vossstef/tang_nano_20k_c64/.assets/dolphin.png

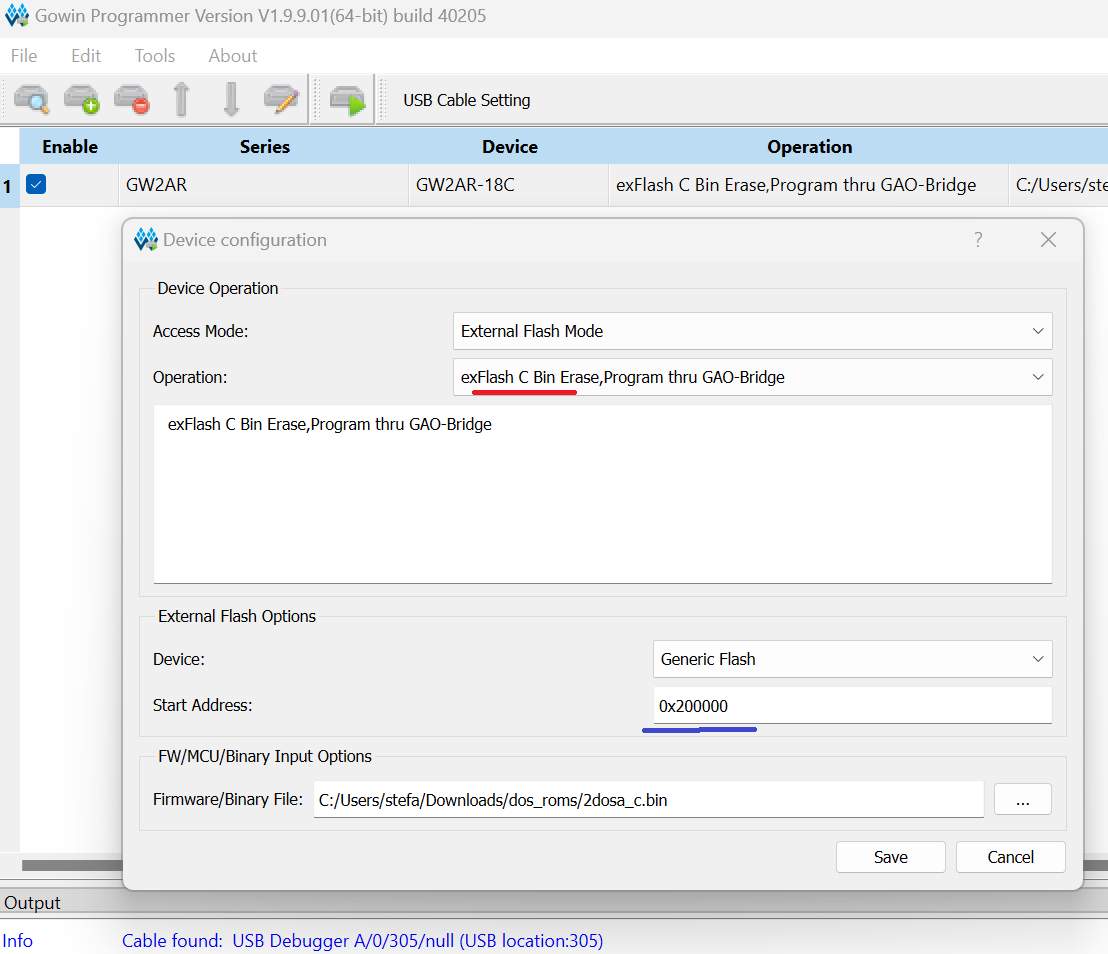
.assets/dolphin.png
