vossstef/tang_nano_20k_c64/.assets/PS_connnector_female.png

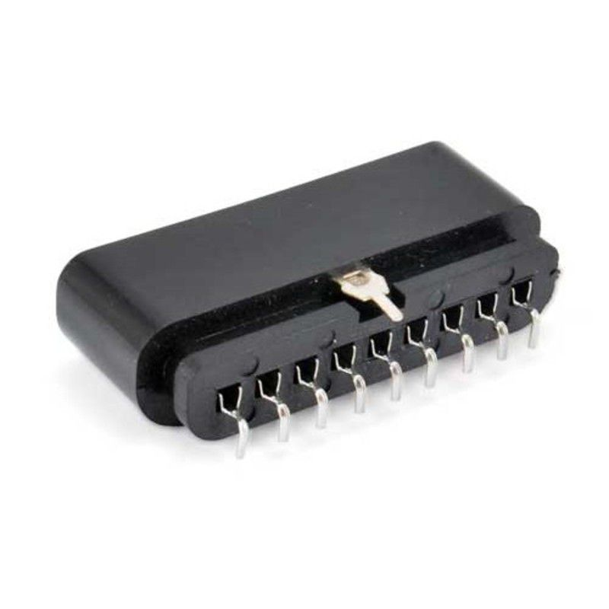
.assets/PS_connnector_female.png
