vossstef/tang_nano_20k_c64/.assets/vic20-Joystick.png

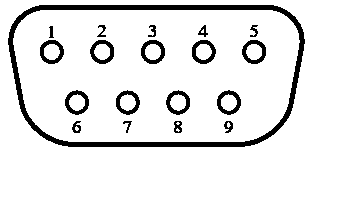
.assets/vic20-Joystick.png
