vossstef/tang_nano_20k_c64/src/fifo_sc_hs/FIFO_SC_HS_Top_gw5a.vhd

--
--Written by GowinSynthesis
--Tool Version "V1.9.9.01"
--Sun May 12 00:47:38 2024

--Source file index table:
--file0 "\/home/vossstef/Dokumente/tang_nano_20k_c64/src/fifo_sc_hs/temp/FIFO_SC/fifo_sc_hs_define.v"
--file1 "\/home/vossstef/Dokumente/tang_nano_20k_c64/src/fifo_sc_hs/temp/FIFO_SC/fifo_sc_hs_parameter.v"
--file2 "\/home/vossstef/Gowin_V1.9.9.01_linux/IDE/ipcore/FIFO_SC_HS/data/fifo_sc_hs.v"
--file3 "\/home/vossstef/Gowin_V1.9.9.01_linux/IDE/ipcore/FIFO_SC_HS/data/fifo_sc_hs_top.v"
`protect begin_protected
`protect version="2.3"
`protect author="default"
`protect author_info="default"
`protect encrypt_agent="GOWIN"
`protect encrypt_agent_info="GOWIN Encrypt Version 2.3"

`protect encoding=(enctype="base64", line_length=76, bytes=256)
`protect key_keyowner="GOWIN",key_keyname="GWK2023-09",key_method="rsa"
`protect key_block
fKtc7d56dFamvtFDO4O6QlQ/mQChC2vDqB9vvZFQsu07QmbTZwBCbHcSg9c2Qbw2vTp5auoD3b91
VnBrmFIJE7ZO6ixMmp+q2YNrsiA/RSfsNSDEhH0vKQw0LDGQ+LaQpbsQsP38Ywhr5HGWnS7MoDNv
HSwKX9g8mJT7/Q4Lo8iNRCs/QKyWcXytIdWEIsB2yFttuY125pkIy0eVJklfc4fd11sZIxdmgucz
9DaDS1XFvY0Kz34P5/p6mjfi3PbE+sys5c+FAVy7ctopbtMai24WShkPhMkbUDM6WWXWU74ohBRx
wu/SC8lLKIqFNhuwDpfDWYbmTo6930i3iSJX9w==

`protect encoding=(enctype="base64", line_length=76, bytes=15648)
`protect data_keyowner="default-ip-vendor"
`protect data_keyname="default-ip-key"
`protect data_method="aes128-cfb"
`protect data_block
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
`protect end_protected
library ieee;
use ieee.std_logic_1164.all;
use ieee.numeric_std.all;
library gw5a;
use gw5a.components.all;

entity FIFO_SC_HS_Top is
port(
  Data :  in std_logic_vector(7 downto 0);
  Clk :  in std_logic;
  WrEn :  in std_logic;
  RdEn :  in std_logic;
  Reset :  in std_logic;
  Q :  out std_logic_vector(7 downto 0);
  Empty :  out std_logic;
  Full :  out std_logic);
end FIFO_SC_HS_Top;
architecture beh of FIFO_SC_HS_Top is
  signal GND_0 : std_logic ;
  signal VCC_0 : std_logic ;
  signal NN : std_logic;
  signal NN_0 : std_logic;
component \~fifo_sc_hs.FIFO_SC_HS_Top\
port(
  Clk: in std_logic;
  Reset: in std_logic;
  VCC_0: in std_logic;
  GND_0: in std_logic;
  WrEn: in std_logic;
  RdEn: in std_logic;
  Data : in std_logic_vector(7 downto 0);
  Full: out std_logic;
  Empty: out std_logic;
  Q : out std_logic_vector(7 downto 0));
end component;
begin
GND_s0: GND
port map (
  G => GND_0);
VCC_s0: VCC
port map (
  V => VCC_0);
GSR_0: GSR
port map (
  GSRI => VCC_0);
fifo_sc_hs_inst: \~fifo_sc_hs.FIFO_SC_HS_Top\
port map(
  Clk => Clk,
  Reset => Reset,
  VCC_0 => VCC_0,
  GND_0 => GND_0,
  WrEn => WrEn,
  RdEn => RdEn,
  Data(7 downto 0) => Data(7 downto 0),
  Full => NN_0,
  Empty => NN,
  Q(7 downto 0) => Q(7 downto 0));
  Empty <= NN;
  Full <= NN_0;
end beh;
