vossstef/tang_nano_20k_c64/src/fifo_sc_hs/fifo_sc_hs.vhd

--
--Written by GowinSynthesis
--Tool Version "V1.9.9.03 (64-bit)"
--Mon Jul  8 15:35:15 2024

--Source file index table:
--file0 "\C:/Users/stefa/Documents/tang_nano_20k_c64/src/fifo_sc_hs/temp/FIFO_SC/fifo_sc_hs_define.v"
--file1 "\C:/Users/stefa/Documents/tang_nano_20k_c64/src/fifo_sc_hs/temp/FIFO_SC/fifo_sc_hs_parameter.v"
--file2 "\C:/Gowin/Gowin_V1.9.9.03_x64/IDE/ipcore/FIFO_SC_HS/data/fifo_sc_hs.v"
--file3 "\C:/Gowin/Gowin_V1.9.9.03_x64/IDE/ipcore/FIFO_SC_HS/data/fifo_sc_hs_top.v"
`protect begin_protected
`protect version="2.3"
`protect author="default"
`protect author_info="default"
`protect encrypt_agent="GOWIN"
`protect encrypt_agent_info="GOWIN Encrypt Version 2.3"

`protect encoding=(enctype="base64", line_length=76, bytes=256)
`protect key_keyowner="GOWIN",key_keyname="GWK2023-09",key_method="rsa"
`protect key_block
EqpCJ1Ww4Pd49B2vVASAo8LpiKKOyOr3fTQtoLEopzYBtsWzW9bwJBFufjYHFtUn8GTtPZPMO28v
8B5rUJs4Hd9uLl1OBi0kSgzbjz0PQjZvvBaG3FrvJm5WkEEgTZf6h/XYErPHf6a9ePw1mQcK/w0V
Tmn92XFVjoSysDTE2lJd41btgDYM6X3vHBOaUt+NLuypAHF27Vg6/a/ukPi+VDsF926BOYJWViP6
U+svy8MhF74v+ClimO5vWuc31+6F3fQYnS+kNuW+etjyU2ZvlGD7zxUmuTqySt4hpy7pKWiCeO8I
zxJ03vHaeP2blj3EFD5TOylCkKAc+X9MKyoI2g==

`protect encoding=(enctype="base64", line_length=76, bytes=12560)
`protect data_keyowner="default-ip-vendor"
`protect data_keyname="default-ip-key"
`protect data_method="aes128-cfb"
`protect data_block
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
cxmnYrtEVBrdJe5dDqL7tjZQre0=
`protect end_protected
library ieee;
use ieee.std_logic_1164.all;
use ieee.numeric_std.all;
library gw2a;
use gw2a.components.all;

entity FIFO_SC_HS_Top is
port(
  Data :  in std_logic_vector(7 downto 0);
  Clk :  in std_logic;
  WrEn :  in std_logic;
  RdEn :  in std_logic;
  Reset :  in std_logic;
  Q :  out std_logic_vector(7 downto 0);
  Empty :  out std_logic;
  Full :  out std_logic);
end FIFO_SC_HS_Top;
architecture beh of FIFO_SC_HS_Top is
  signal Clk_d : std_logic ;
  signal WrEn_d : std_logic ;
  signal RdEn_d : std_logic ;
  signal Reset_d : std_logic ;
  signal GND_0 : std_logic ;
  signal VCC_0 : std_logic ;
  signal Full_d : std_logic ;
  signal Empty_d : std_logic ;
  signal Data_d : std_logic_vector(7 downto 0);
  signal Q_d : std_logic_vector(7 downto 0);
component \~fifo_sc_hs.FIFO_SC_HS_Top\
port(
  Clk_d: in std_logic;
  Reset_d: in std_logic;
  GND_0: in std_logic;
  VCC_0: in std_logic;
  WrEn_d: in std_logic;
  RdEn_d: in std_logic;
  Data_d : in std_logic_vector(7 downto 0);
  Full_d: out std_logic;
  Empty_d: out std_logic;
  Q_d : out std_logic_vector(7 downto 0));
end component;
begin
Data_0_ibuf: IBUF
port map (
  O => Data_d(0),
  I => Data(0));
Data_1_ibuf: IBUF
port map (
  O => Data_d(1),
  I => Data(1));
Data_2_ibuf: IBUF
port map (
  O => Data_d(2),
  I => Data(2));
Data_3_ibuf: IBUF
port map (
  O => Data_d(3),
  I => Data(3));
Data_4_ibuf: IBUF
port map (
  O => Data_d(4),
  I => Data(4));
Data_5_ibuf: IBUF
port map (
  O => Data_d(5),
  I => Data(5));
Data_6_ibuf: IBUF
port map (
  O => Data_d(6),
  I => Data(6));
Data_7_ibuf: IBUF
port map (
  O => Data_d(7),
  I => Data(7));
Clk_ibuf: IBUF
port map (
  O => Clk_d,
  I => Clk);
WrEn_ibuf: IBUF
port map (
  O => WrEn_d,
  I => WrEn);
RdEn_ibuf: IBUF
port map (
  O => RdEn_d,
  I => RdEn);
Reset_ibuf: IBUF
port map (
  O => Reset_d,
  I => Reset);
Q_0_obuf: OBUF
port map (
  O => Q(0),
  I => Q_d(0));
Q_1_obuf: OBUF
port map (
  O => Q(1),
  I => Q_d(1));
Q_2_obuf: OBUF
port map (
  O => Q(2),
  I => Q_d(2));
Q_3_obuf: OBUF
port map (
  O => Q(3),
  I => Q_d(3));
Q_4_obuf: OBUF
port map (
  O => Q(4),
  I => Q_d(4));
Q_5_obuf: OBUF
port map (
  O => Q(5),
  I => Q_d(5));
Q_6_obuf: OBUF
port map (
  O => Q(6),
  I => Q_d(6));
Q_7_obuf: OBUF
port map (
  O => Q(7),
  I => Q_d(7));
Empty_obuf: OBUF
port map (
  O => Empty,
  I => Empty_d);
Full_obuf: OBUF
port map (
  O => Full,
  I => Full_d);
GND_s0: GND
port map (
  G => GND_0);
VCC_s0: VCC
port map (
  V => VCC_0);
GSR_0: GSR
port map (
  GSRI => VCC_0);
fifo_sc_hs_inst: \~fifo_sc_hs.FIFO_SC_HS_Top\
port map(
  Clk_d => Clk_d,
  Reset_d => Reset_d,
  GND_0 => GND_0,
  VCC_0 => VCC_0,
  WrEn_d => WrEn_d,
  RdEn_d => RdEn_d,
  Data_d(7 downto 0) => Data_d(7 downto 0),
  Full_d => Full_d,
  Empty_d => Empty_d,
  Q_d(7 downto 0) => Q_d(7 downto 0));
end beh;
