vossstef/tang_nano_20k_c64/src/sid/sid_tables.sv

module sid_tables
#(
	parameter MULTI_FILTERS   = 1
)
(
	input             clock,
	input             mode,

	// waves
	input      [11:0] acc_t,
	output reg  [7:0] _st_out,
	output reg  [7:0] p_t_out,
	output reg  [7:0] ps__out,
	output reg  [7:0] pst_out,

	// filter
	input       [1:0] cfg,
	input      [10:0] Fc,
	input      [12:0] Fc_offset,
	output     [15:0] F0,
	input             ld_clk,
	input      [11:0] ld_addr,
	input      [15:0] ld_data,
	input             ld_wr
);

// P + T
always_ff @(posedge clock) begin
	p_t_out <= mode ? wave8580_p_t[acc_t[10:0]] : wave6581_p_t[acc_t[10:0]];
end

// P + S
always_ff @(posedge clock) begin
	ps__out <= mode ? wave8580_ps_[acc_t] : wave6581_ps_[acc_t[10:0]];
end

// S + T
always_ff @(posedge clock) begin
	_st_out <= mode ? {
		((acc_t & 'he7e) == 'he7e) | ((acc_t & 'he80) == 'he80) | ((acc_t & 'hf00) == 'hf00) | ((acc_t & 'he7d) == 'he7d),
		((acc_t & 'h7f8) == 'h7f8) | ((acc_t & 'hf00) == 'hf00),
		((acc_t & 'h7e0) == 'h7e0) | ((acc_t & 'hf0f) == 'hf0f) | ((acc_t & 'hf1b) == 'hf1b) | ((acc_t & 'hbfe) == 'hbfe) | ((acc_t & 'hf1e) == 'hf1e) | ((acc_t & 'hf40) == 'hf40) | ((acc_t & 'hf30) == 'hf30) | ((acc_t & 'hf29) == 'hf29) | ((acc_t & 'hf26) == 'hf26) | ((acc_t & 'hf80) == 'hf80),
		((acc_t & 'h7e0) == 'h7e0) | ((acc_t & 'h3f0) == 'h3f0) | ((acc_t & 'hdfe) == 'hdfe) | ((acc_t & 'h5ff) == 'h5ff) | ((acc_t & 'hf80) == 'hf80),
		((acc_t & 'h7e0) == 'h7e0) | ((acc_t & 'h3f0) == 'h3f0) | ((acc_t & 'hfc0) == 'hfc0) | ((acc_t & 'h1f8) == 'h1f8) | ((acc_t & 'heff) == 'heff),
		((acc_t & 'h0fc) == 'h0fc) | ((acc_t & 'h1f8) == 'h1f8) | ((acc_t & 'h3f0) == 'h3f0) | ((acc_t & 'hfe0) == 'hfe0),
		((acc_t & 'h07e) == 'h07e) | ((acc_t & 'hff0) == 'hff0) | ((acc_t & 'h7f7) == 'h7f7) | ((acc_t & 'h1f8) == 'h1f8) | ((acc_t & 'h0fc) == 'h0fc),
		((acc_t & 'hdbf) == 'hdbf) | ((acc_t & 'h0fc) == 'h0fc) | ((acc_t & 'h3fa) == 'h3fa) | ((acc_t & 'h7f8) == 'h7f8) | ((acc_t & 'h3bf) == 'h3bf) | ((acc_t & 'h07e) == 'h07e)
	} : {
		1'b0,
		((acc_t & 'h7fc) == 'h7fc),
		((acc_t & 'h7e0) == 'h7e0) | ((acc_t & 'h3fe) == 'h3fe),
		((acc_t & 'h7e0) == 'h7e0) | ((acc_t & 'h5ff) == 'h5ff) | ((acc_t & 'h3f0) == 'h3f0),
		((acc_t & 'h7e0) == 'h7e0) | ((acc_t & 'h1f8) == 'h1f8) | ((acc_t & 'h3f0) == 'h3f0),
		((acc_t & 'h0fc) == 'h0fc) | ((acc_t & 'h1f8) == 'h1f8) | ((acc_t & 'h3f0) == 'h3f0),
		((acc_t & 'h07e) == 'h07e) | ((acc_t & 'h1f8) == 'h1f8) | ((acc_t & 'h0fc) == 'h0fc),
		((acc_t & 'h13f) == 'h13f) | ((acc_t & 'h07e) == 'h07e) | ((acc_t & 'h7fa) == 'h7fa) | ((acc_t & 'h0bf) == 'h0bf) | ((acc_t & 'h0fc) == 'h0fc)
	};
end

// P + S + T
always_ff @(posedge clock) begin
	pst_out <= mode ? {
		((acc_t & 'he89) == 'he89) | ((acc_t & 'he3e) == 'he3e) | ((acc_t & 'hec0) == 'hec0) | ((acc_t & 'he8a) == 'he8a) | ((acc_t & 'hdf7) == 'hdf7) | ((acc_t & 'hdf8) == 'hdf8) | ((acc_t & 'he85) == 'he85) | ((acc_t & 'he6a) == 'he6a) | ((acc_t & 'he90) == 'he90) | ((acc_t & 'he83) == 'he83) | ((acc_t & 'he67) == 'he67) | ((acc_t & 'hea0) == 'hea0) | ((acc_t & 'hf00) == 'hf00) | ((acc_t & 'he5e) == 'he5e) | ((acc_t & 'he70) == 'he70) | ((acc_t & 'he6c) == 'he6c),
		((acc_t & 'heee) == 'heee) | ((acc_t & 'h7ef) == 'h7ef) | ((acc_t & 'h7f2) == 'h7f2) | ((acc_t & 'h7f4) == 'h7f4) | ((acc_t & 'hef0) == 'hef0) | ((acc_t & 'h7f8) == 'h7f8) | ((acc_t & 'hf00) == 'hf00) | ((acc_t & 'h7f1) == 'h7f1),
		((acc_t & 'hf78) == 'hf78) | ((acc_t & 'h7f0) == 'h7f0) | ((acc_t & 'h7ee) == 'h7ee) | ((acc_t & 'hf74) == 'hf74) | ((acc_t & 'hf6f) == 'hf6f) | ((acc_t & 'hf80) == 'hf80) | ((acc_t & 'hbff) == 'hbff),
		((acc_t & 'hdff) == 'hdff) | ((acc_t & 'hbfe) == 'hbfe) | ((acc_t & 'h7ef) == 'h7ef) | ((acc_t & 'h7f2) == 'h7f2) | ((acc_t & 'h3ff) == 'h3ff) | ((acc_t & 'h7f4) == 'h7f4) | ((acc_t & 'hfc0) == 'hfc0) | ((acc_t & 'hfb8) == 'hfb8) | ((acc_t & 'h7f8) == 'h7f8) | ((acc_t & 'hfb6) == 'hfb6),
		((acc_t & 'hbfe) == 'hbfe) | ((acc_t & 'hfdc) == 'hfdc) | ((acc_t & 'hdfe) == 'hdfe) | ((acc_t & 'h7f7) == 'h7f7) | ((acc_t & 'hfda) == 'hfda) | ((acc_t & 'hbfd) == 'hbfd) | ((acc_t & 'h7f8) == 'h7f8) | ((acc_t & 'h3ff) == 'h3ff) | ((acc_t & 'hfe0) == 'hfe0) | ((acc_t & 'heff) == 'heff),
		((acc_t & 'hfeb) == 'hfeb) | ((acc_t & 'h7fa) == 'h7fa) | ((acc_t & 'hbfe) == 'hbfe) | ((acc_t & 'hdfe) == 'hdfe) | ((acc_t & 'hff0) == 'hff0) | ((acc_t & 'h7fc) == 'h7fc) | ((acc_t & 'h3ff) == 'h3ff) | ((acc_t & 'hfec) == 'hfec) | ((acc_t & 'heff) == 'heff),
		((acc_t & 'hff6) == 'hff6) | ((acc_t & 'hdff) == 'hdff) | ((acc_t & 'hf7f) == 'hf7f) | ((acc_t & 'hbfe) == 'hbfe) | ((acc_t & 'h7fc) == 'h7fc) | ((acc_t & 'hff5) == 'hff5) | ((acc_t & 'h3ff) == 'h3ff) | ((acc_t & 'hff8) == 'hff8) | ((acc_t & 'heff) == 'heff),
		((acc_t & 'hdff) == 'hdff) | ((acc_t & 'hf7f) == 'hf7f) | ((acc_t & 'hffa) == 'hffa) | ((acc_t & 'h7fe) == 'h7fe) | ((acc_t & 'hff9) == 'hff9) | ((acc_t & 'hffc) == 'hffc) | ((acc_t & 'h3ff) == 'h3ff) | ((acc_t & 'heff) == 'heff)
	} : {
		1'b0,
		((acc_t & 'h7fc) == 'h7fc) | ((acc_t & 'h7fb) == 'h7fb),
		((acc_t & 'h7ef) == 'h7ef) | ((acc_t & 'h7f7) == 'h7f7) | ((acc_t & 'h7fc) == 'h7fc) | ((acc_t & 'h7fb) == 'h7fb) | ((acc_t & 'h3ff) == 'h3ff),
		((acc_t & 'h7fc) == 'h7fc) | ((acc_t & 'h3ff) == 'h3ff) | ((acc_t & 'h7f7) == 'h7f7) | ((acc_t & 'h7fb) == 'h7fb),
		((acc_t & 'h7fc) == 'h7fc) | ((acc_t & 'h3ff) == 'h3ff) | ((acc_t & 'h7fb) == 'h7fb),
		((acc_t & 'h7fd) == 'h7fd) | ((acc_t & 'h3ff) == 'h3ff) | ((acc_t & 'h7fe) == 'h7fe),
		((acc_t & 'h7fd) == 'h7fd) | ((acc_t & 'h3ff) == 'h3ff) | ((acc_t & 'h7fe) == 'h7fe),
		((acc_t & 'h3ff) == 'h3ff) | ((acc_t & 'h7fe) == 'h7fe)
	};
end


wire [7:0] wave6581_p_t[0:2047] = 
'{
	'h00, 'h00, 'h00, 'h00, 'h00, 'h00, 'h00, 'h00, 'h00, 'h00, 'h00, 'h00, 'h00, 'h00, 'h00, 'h00,
	'h00, 'h00, 'h00, 'h00, 'h00, 'h00, 'h00, 'h00, 'h00, 'h00, 'h00, 'h00, 'h00, 'h00, 'h00, 'h00,
	'h00, 'h00, 'h00, 'h00, 'h00, 'h00, 'h00, 'h00, 'h00, 'h00, 'h00, 'h00, 'h00, 'h00, 'h00, 'h00,
	'h00, 'h00, 'h00, 'h00, 'h00, 'h00, 'h00, 'h00, 'h00, 'h00, 'h00, 'h00, 'h00, 'h00, 'h00, 'h00,
	'h00, 'h00, 'h00, 'h00, 'h00, 'h00, 'h00, 'h00, 'h00, 'h00, 'h00, 'h00, 'h00, 'h00, 'h00, 'h00,
	'h00, 'h00, 'h00, 'h00, 'h00, 'h00, 'h00, 'h00, 'h00, 'h00, 'h00, 'h00, 'h00, 'h00, 'h00, 'h00,
	'h00, 'h00, 'h00, 'h00, 'h00, 'h00, 'h00, 'h00, 'h00, 'h00, 'h00, 'h00, 'h00, 'h00, 'h00, 'h00,
	'h00, 'h00, 'h00, 'h00, 'h00, 'h00, 'h00, 'h00, 'h00, 'h00, 'h00, 'h00, 'h00, 'h00, 'h00, 'h00,
	'h00, 'h00, 'h00, 'h00, 'h00, 'h00, 'h00, 'h00, 'h00, 'h00, 'h00, 'h00, 'h00, 'h00, 'h00, 'h00,
	'h00, 'h00, 'h00, 'h00, 'h00, 'h00, 'h00, 'h00, 'h00, 'h00, 'h00, 'h00, 'h00, 'h00, 'h00, 'h00,
	'h00, 'h00, 'h00, 'h00, 'h00, 'h00, 'h00, 'h00, 'h00, 'h00, 'h00, 'h00, 'h00, 'h00, 'h00, 'h00,
	'h00, 'h00, 'h00, 'h00, 'h00, 'h00, 'h00, 'h00, 'h00, 'h00, 'h00, 'h00, 'h00, 'h00, 'h00, 'h00,
	'h00, 'h00, 'h00, 'h00, 'h00, 'h00, 'h00, 'h00, 'h00, 'h00, 'h00, 'h00, 'h00, 'h00, 'h00, 'h00,
	'h00, 'h00, 'h00, 'h00, 'h00, 'h00, 'h00, 'h00, 'h00, 'h00, 'h00, 'h00, 'h00, 'h00, 'h00, 'h00,
	'h00, 'h00, 'h00, 'h00, 'h00, 'h00, 'h00, 'h00, 'h00, 'h00, 'h00, 'h00, 'h00, 'h00, 'h00, 'h00,
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
	'h00, 'h00, 'h00, 'h00, 'h00, 'h00, 'h00, 'h00, 'h00, 'h00, 'h00, 'h00, 'h00, 'h00, 'h00, 'h80,
	'h00, 'h00, 'h00, 'h00, 'h00, 'h00, 'h00, 'h80, 'h00, 'h00, 'h00, 'h80, 'h00, 'h80, 'h80, 'hc0,
	'h00, 'h00, 'h00, 'h00, 'h00, 'h00, 'h00, 'h80, 'h00, 'h00, 'h00, 'h80, 'h00, 'h80, 'h80, 'hc0,
	'h00, 'h00, 'h00, 'h80, 'h00, 'h80, 'hc0, 'hc0, 'h80, 'hc0, 'hc0, 'hc0, 'hc0, 'hc0, 'hd0, 'hd7,
	'h00, 'h00, 'h00, 'h00, 'h00, 'h00, 'h00, 'h80, 'h00, 'h00, 'h00, 'h80, 'h80, 'h80, 'hc0, 'hc0,
	'h00, 'h80, 'h80, 'hc0, 'h80, 'hc0, 'hc0, 'hc0, 'h80, 'hc0, 'hc0, 'hc0, 'hc0, 'hd0, 'hd0, 'hdb,
	'h00, 'h80, 'h80, 'hc0, 'h80, 'hc0, 'hc0, 'hd0, 'h80, 'hc0, 'hc0, 'hd0, 'hc0, 'hd0, 'hd8, 'hdd,
	'hc0, 'hc0, 'hc0, 'hd0, 'hc0, 'hd8, 'hd8, 'hde, 'hc0, 'hd8, 'hdc, 'hdf, 'hdc, 'hdf, 'hdf, 'hdf,
	'h00, 'h00, 'h00, 'h00, 'h00, 'h00, 'h00, 'h00, 'h00, 'h00, 'h00, 'h00, 'h00, 'h00, 'h00, 'h80,
	'h00, 'h00, 'h00, 'h00, 'h00, 'h00, 'h00, 'h80, 'h00, 'h00, 'h00, 'h80, 'h80, 'hc0, 'hc0, 'he0,
	'h00, 'h00, 'h00, 'h00, 'h00, 'h00, 'h00, 'h80, 'h00, 'h80, 'h80, 'hc0, 'h80, 'hc0, 'hc0, 'he0,
	'h00, 'h80, 'h80, 'hc0, 'h80, 'hc0, 'hc0, 'he0, 'h80, 'hc0, 'hc0, 'he0, 'hc0, 'he0, 'he0, 'he7,
	'h00, 'h00, 'h00, 'h80, 'h00, 'h80, 'h80, 'hc0, 'h00, 'h80, 'h80, 'hc0, 'h80, 'hc0, 'hc0, 'he0,
	'h00, 'h80, 'h80, 'hc0, 'h80, 'hc0, 'hc0, 'he0, 'hc0, 'hc0, 'hc0, 'he0, 'he0, 'he0, 'he0, 'heb,
	'h80, 'h80, 'hc0, 'hc0, 'hc0, 'hc0, 'hc0, 'he0, 'hc0, 'he0, 'he0, 'he0, 'he0, 'he0, 'he0, 'hed,
	'hc0, 'he0, 'he0, 'he0, 'he0, 'he8, 'he8, 'hee, 'he0, 'he8, 'hec, 'hef, 'hec, 'hef, 'hef, 'hef,
	'h00, 'h00, 'h00, 'h80, 'h80, 'h80, 'h80, 'hc0, 'h80, 'h80, 'hc0, 'hc0, 'hc0, 'hc0, 'hc0, 'hf0,
	'h80, 'hc0, 'hc0, 'hc0, 'hc0, 'he0, 'he0, 'hf0, 'hc0, 'he0, 'he0, 'hf0, 'he0, 'hf0, 'hf0, 'hf3,
	'h80, 'hc0, 'hc0, 'he0, 'hc0, 'he0, 'he0, 'hf0, 'hc0, 'he0, 'he0, 'hf0, 'he0, 'hf0, 'hf0, 'hf5,
	'he0, 'he0, 'he0, 'hf0, 'hf0, 'hf0, 'hf0, 'hf6, 'hf0, 'hf0, 'hf4, 'hf7, 'hf4, 'hf7, 'hf7, 'hf7,
	'hc0, 'hc0, 'hc0, 'he0, 'he0, 'he0, 'he0, 'hf0, 'he0, 'he0, 'he0, 'hf8, 'hf0, 'hf8, 'hf8, 'hf9,
	'he0, 'hf0, 'hf0, 'hf8, 'hf0, 'hf8, 'hf8, 'hfa, 'hf0, 'hf8, 'hf8, 'hfb, 'hf8, 'hfb, 'hfb, 'hfb,
	'he0, 'hf0, 'hf0, 'hf8, 'hf0, 'hf8, 'hfc, 'hfc, 'hf8, 'hfc, 'hfc, 'hfd, 'hfc, 'hfd, 'hfd, 'hfd,
	'hf8, 'hfc, 'hfe, 'hfe, 'hfe, 'hfe, 'hfe, 'hfe, 'hfe, 'hff, 'hff, 'hff, 'hff, 'hff, 'hff, 'hff
};


wire [7:0] wave6581_ps_[0:2047] = 
'{
	'h00, 'h00, 'h00, 'h00, 'h00, 'h00, 'h00, 'h00, 'h00, 'h00, 'h00, 'h00, 'h00, 'h00, 'h00, 'h00,
	'h00, 'h00, 'h00, 'h00, 'h00, 'h00, 'h00, 'h00, 'h00, 'h00, 'h00, 'h00, 'h00, 'h00, 'h00, 'h00,
	'h00, 'h00, 'h00, 'h00, 'h00, 'h00, 'h00, 'h00, 'h00, 'h00, 'h00, 'h00, 'h00, 'h00, 'h00, 'h00,
	'h00, 'h00, 'h00, 'h00, 'h00, 'h00, 'h00, 'h00, 'h00, 'h00, 'h00, 'h00, 'h00, 'h00, 'h00, 'h00,
	'h00, 'h00, 'h00, 'h00, 'h00, 'h00, 'h00, 'h00, 'h00, 'h00, 'h00, 'h00, 'h00, 'h00, 'h00, 'h00,
	'h00, 'h00, 'h00, 'h00, 'h00, 'h00, 'h00, 'h00, 'h00, 'h00, 'h00, 'h00, 'h00, 'h00, 'h00, 'h00,
	'h00, 'h00, 'h00, 'h00, 'h00, 'h00, 'h00, 'h00, 'h00, 'h00, 'h00, 'h00, 'h00, 'h00, 'h00, 'h00,
	'h00, 'h00, 'h00, 'h00, 'h00, 'h00, 'h00, 'h00, 'h00, 'h00, 'h00, 'h00, 'h00, 'h00, 'h00, 'h00,
	'h00, 'h00, 'h00, 'h00, 'h00, 'h00, 'h00, 'h00, 'h00, 'h00, 'h00, 'h00, 'h00, 'h00, 'h00, 'h00,
	'h00, 'h00, 'h00, 'h00, 'h00, 'h00, 'h00, 'h00, 'h00, 'h00, 'h00, 'h00, 'h00, 'h00, 'h00, 'h00,
	'h00, 'h00, 'h00, 'h00, 'h00, 'h00, 'h00, 'h00, 'h00, 'h00, 'h00, 'h00, 'h00, 'h00, 'h00, 'h00,
	'h00, 'h00, 'h00, 'h00, 'h00, 'h00, 'h00, 'h00, 'h00, 'h00, 'h00, 'h00, 'h00, 'h00, 'h00, 'h00,
	'h00, 'h00, 'h00, 'h00, 'h00, 'h00, 'h00, 'h00, 'h00, 'h00, 'h00, 'h00, 'h00, 'h00, 'h00, 'h00,
	'h00, 'h00, 'h00, 'h00, 'h00, 'h00, 'h00, 'h00, 'h00, 'h00, 'h00, 'h00, 'h00, 'h00, 'h00, 'h00,
	'h00, 'h00, 'h00, 'h00, 'h00, 'h00, 'h00, 'h00, 'h00, 'h00, 'h00, 'h00, 'h00, 'h00, 'h00, 'h00,
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
	'h80, 'h80, 'h80, 'h80, 'h80, 'h80, 'h80, 'h80, 'h80, 'h80, 'h80, 'h80, 'h80, 'h80, 'h80, 'hc0,
	'h80, 'h80, 'h80, 'h80, 'h80, 'h80, 'hc0, 'hc0, 'h80, 'hc0, 'hc0, 'hc0, 'hc0, 'hc0, 'hc0, 'hc3,
	'h80, 'h80, 'h80, 'h80, 'h80, 'h80, 'h80, 'hc0, 'h80, 'h80, 'h80, 'hc0, 'h80, 'hc0, 'hc0, 'hc0,
	'h80, 'hc0, 'hc0, 'hc0, 'hc0, 'hc0, 'hc0, 'hc0, 'hc0, 'hc0, 'hc0, 'hc0, 'hc0, 'hc0, 'hc0, 'hc1,
	'hc0, 'hc0, 'hc0, 'hc0, 'hc0, 'hc0, 'hc0, 'hc0, 'hc0, 'hc0, 'hc0, 'hc0, 'hc0, 'hc0, 'hc0, 'hc0,
	'hc0, 'hc0, 'hc0, 'hc0, 'hc0, 'hc0, 'hc0, 'hc0, 'hc0, 'hc0, 'hc0, 'hc0, 'hc0, 'hc1, 'hc7, 'hd7,
	'hc0, 'hc0, 'hc0, 'hc0, 'hc0, 'hc0, 'hc0, 'hc0, 'hc0, 'hc0, 'hc0, 'hc0, 'hc0, 'hc0, 'hc0, 'hc0,
	'hc0, 'hc0, 'hc0, 'hc0, 'hc0, 'hc0, 'hc0, 'hc0, 'hc0, 'hc0, 'hc0, 'hc0, 'hc0, 'hc0, 'hc0, 'hc0,
	'hc0, 'hc0, 'hc0, 'hc0, 'hc0, 'hc0, 'hc0, 'hc0, 'hc0, 'hc0, 'hc0, 'hc0, 'hc0, 'hc0, 'hc0, 'hd0,
	'hc0, 'hc0, 'hc0, 'hc0, 'hc0, 'hc0, 'hc0, 'hd0, 'hc0, 'hc0, 'hc0, 'hd0, 'hc0, 'hd0, 'hd8, 'hdb,
	'hc0, 'hc0, 'hc0, 'hc0, 'hc0, 'hc0, 'hc0, 'hc0, 'hc0, 'hc0, 'hc0, 'hc0, 'hc0, 'hc0, 'hc0, 'hd8,
	'hc0, 'hc0, 'hc0, 'hc0, 'hc0, 'hc0, 'hc0, 'hd8, 'hc0, 'hc0, 'hc0, 'hd8, 'hd0, 'hd8, 'hd8, 'hdd,
	'hc0, 'hc0, 'hc0, 'hd0, 'hc0, 'hd0, 'hd0, 'hdc, 'hd0, 'hd8, 'hd8, 'hdc, 'hd8, 'hdc, 'hdc, 'hde,
	'hd8, 'hdc, 'hdc, 'hde, 'hdc, 'hde, 'hde, 'hdf, 'hde, 'hdf, 'hdf, 'hdf, 'hdf, 'hdf, 'hdf, 'hdf,
	'hc0, 'hc0, 'hc0, 'hc0, 'hc0, 'hc0, 'hc0, 'hc0, 'hc0, 'hc0, 'hc0, 'hc0, 'hc0, 'hc0, 'hc0, 'hc0,
	'hc0, 'hc0, 'hc0, 'hc0, 'hc0, 'hc0, 'hc0, 'hc0, 'hc0, 'hc0, 'hc0, 'hc0, 'hc0, 'hc0, 'hc0, 'hc0,
	'hc0, 'hc0, 'hc0, 'hc0, 'hc0, 'hc0, 'hc0, 'hc0, 'hc0, 'hc0, 'hc0, 'hc0, 'hc0, 'hc0, 'hc0, 'hc0,
	'hc0, 'hc0, 'hc0, 'hc0, 'hc0, 'hc0, 'hc0, 'hc0, 'hc0, 'hc0, 'hc0, 'hc0, 'hc0, 'hc0, 'hc0, 'he3,
	'hc0, 'hc0, 'hc0, 'hc0, 'hc0, 'hc0, 'hc0, 'hc0, 'hc0, 'hc0, 'hc0, 'hc0, 'hc0, 'hc0, 'hc0, 'hc0,
	'hc0, 'hc0, 'hc0, 'hc0, 'hc0, 'hc0, 'hc0, 'he0, 'hc0, 'hc0, 'hc0, 'he0, 'hc0, 'he0, 'he0, 'he1,
	'hc0, 'hc0, 'hc0, 'hc0, 'hc0, 'hc0, 'hc0, 'he0, 'hc0, 'hc0, 'hc0, 'he0, 'he0, 'he0, 'he0, 'he0,
	'hc0, 'he0, 'he0, 'he0, 'he0, 'he0, 'he0, 'he0, 'he0, 'he0, 'he0, 'he0, 'he0, 'he1, 'he3, 'he7,
	'hc0, 'hc0, 'hc0, 'hc0, 'hc0, 'hc0, 'hc0, 'he0, 'hc0, 'hc0, 'hc0, 'he0, 'hc0, 'he0, 'he0, 'he0,
	'hc0, 'hc0, 'hc0, 'he0, 'hc0, 'he0, 'he0, 'he0, 'he0, 'he0, 'he0, 'he0, 'he0, 'he0, 'he0, 'he0,
	'he0, 'he0, 'he0, 'he0, 'he0, 'he0, 'he0, 'he0, 'he0, 'he0, 'he0, 'he0, 'he0, 'he0, 'he0, 'he0,
	'he0, 'he0, 'he0, 'he0, 'he0, 'he0, 'he0, 'he0, 'he0, 'he0, 'he0, 'he0, 'he0, 'he0, 'he0, 'heb,
	'he0, 'he0, 'he0, 'he0, 'he0, 'he0, 'he0, 'he0, 'he0, 'he0, 'he0, 'he0, 'he0, 'he0, 'he0, 'he0,
	'he0, 'he0, 'he0, 'he0, 'he0, 'he0, 'he0, 'he0, 'he0, 'he0, 'he0, 'he8, 'he0, 'he8, 'he8, 'hed,
	'he0, 'he0, 'he0, 'he0, 'he0, 'he0, 'he0, 'hec, 'he0, 'he0, 'he0, 'hec, 'he8, 'hec, 'hec, 'hee,
	'he8, 'he8, 'he8, 'hec, 'hec, 'hee, 'hee, 'hef, 'hec, 'hef, 'hef, 'hef, 'hef, 'hef, 'hef, 'hef,
	'he0, 'he0, 'he0, 'he0, 'he0, 'he0, 'he0, 'he0, 'he0, 'he0, 'he0, 'he0, 'he0, 'he0, 'he0, 'he0,
	'he0, 'he0, 'he0, 'he0, 'he0, 'he0, 'he0, 'he0, 'he0, 'he0, 'he0, 'he0, 'he0, 'he0, 'he0, 'hf0,
	'he0, 'he0, 'he0, 'he0, 'he0, 'he0, 'he0, 'hf0, 'he0, 'he0, 'he0, 'hf0, 'he0, 'hf0, 'hf0, 'hf0,
	'he0, 'he0, 'he0, 'hf0, 'hf0, 'hf0, 'hf0, 'hf0, 'hf0, 'hf0, 'hf0, 'hf0, 'hf0, 'hf0, 'hf0, 'hf3,
	'he0, 'he0, 'he0, 'hf0, 'hf0, 'hf0, 'hf0, 'hf0, 'hf0, 'hf0, 'hf0, 'hf0, 'hf0, 'hf0, 'hf0, 'hf0,
	'hf0, 'hf0, 'hf0, 'hf0, 'hf0, 'hf0, 'hf0, 'hf0, 'hf0, 'hf0, 'hf0, 'hf0, 'hf0, 'hf0, 'hf0, 'hf5,
	'hf0, 'hf0, 'hf0, 'hf0, 'hf0, 'hf0, 'hf0, 'hf0, 'hf0, 'hf0, 'hf0, 'hf0, 'hf0, 'hf4, 'hf4, 'hf6,
	'hf0, 'hf0, 'hf0, 'hf4, 'hf0, 'hf4, 'hf6, 'hf7, 'hf4, 'hf6, 'hf6, 'hf7, 'hf7, 'hf7, 'hf7, 'hf7,
	'hf0, 'hf0, 'hf0, 'hf0, 'hf0, 'hf0, 'hf0, 'hf8, 'hf0, 'hf0, 'hf0, 'hf0, 'hf0, 'hf8, 'hf8, 'hf8,
	'hf0, 'hf0, 'hf0, 'hf8, 'hf0, 'hf8, 'hf8, 'hf8, 'hf8, 'hf8, 'hf8, 'hf8, 'hf8, 'hf8, 'hf8, 'hf9,
	'hf8, 'hf8, 'hf8, 'hf8, 'hf8, 'hf8, 'hf8, 'hf8, 'hf8, 'hf8, 'hf8, 'hf8, 'hf8, 'hf8, 'hf8, 'hfa,
	'hf8, 'hf8, 'hf8, 'hf8, 'hf8, 'hf8, 'hf8, 'hfb, 'hf8, 'hfa, 'hfa, 'hfb, 'hfb, 'hfb, 'hfb, 'hfb,
	'hf8, 'hf8, 'hf8, 'hfc, 'hf8, 'hfc, 'hfc, 'hfc, 'hfc, 'hfc, 'hfc, 'hfc, 'hfc, 'hfc, 'hfc, 'hfc,
	'hfc, 'hfc, 'hfc, 'hfc, 'hfc, 'hfc, 'hfc, 'hfd, 'hfc, 'hfc, 'hfc, 'hfd, 'hfd, 'hfd, 'hfd, 'hfd,
	'hfc, 'hfc, 'hfe, 'hfe, 'hfe, 'hfe, 'hfe, 'hfe, 'hfe, 'hfe, 'hfe, 'hfe, 'hfe, 'hfe, 'hfe, 'hfe,
	'hff, 'hff, 'hff, 'hff, 'hff, 'hff, 'hff, 'hff, 'hff, 'hff, 'hff, 'hff, 'hff, 'hff, 'hff, 'hff
};


/////////////////////////////////////////////////////////////////////////////////////


reg [15:0] f0;
generate
	if(MULTI_FILTERS) begin
		always_ff @(posedge ld_clk) if(ld_wr) f6581_curve[1024+ld_addr] <= ld_data;
		always_ff @(posedge clock) f0 <= f6581_curve[{cfg, Fc[10:1]}];
	end
	else begin
		always_ff @(posedge ld_clk) if(ld_wr) f6581_curve[ld_addr[9:0]] <= ld_data;
		always_ff @(posedge clock) f0 <= f6581_curve[Fc[10:1]];
	end
endgenerate

wire [10:0] fc_6581;
sid_dac #(.BITS(11)) fc_dac
(
  .vin  (Fc),
  .vout (fc_6581)
);

function reg [9:0] tanh_x_mirror(signed [10:0] x);
    tanh_x_mirror = 10'(x < 0 ? -x : x);
endfunction

function signed [10:0] tanh_x_clamp(signed [12:0] x);
    tanh_x_clamp = (x < -1023) ? -11'sd1023 :
                   (x >  1023) ?  11'sd1023 :
                   11'(x);
endfunction

function signed [15:0] tanh_y_mirror(logic x_neg,signed [15:0] y);
    tanh_y_mirror = x_neg ? -y : y;
endfunction

wire signed [15:0] f6581_adj_y0 = 16'(9883+250);
wire [10:0] fc_x = tanh_x_clamp(13'(fc_6581) - Fc_offset);

reg [15:0] f0_adj;
always_ff @(posedge clock) f0_adj <= {fc_x[10], f6581_adj[tanh_x_mirror(fc_x)]};

assign F0 = mode ? ({ 3'b000, Fc, 2'b00 } + Fc) : Fc_offset ? (f6581_adj_y0 + tanh_y_mirror(f0_adj[15], f0_adj[14:0])) : {1'b0, f0[15:1]};

// value = pi * 1.048576 * f0[fc]
reg  [15:0] f6581_curve[4*1024] =
'{
	// 0 mixed calc 
      933,    932,    932,    933,    936,    937,    943,    948,
      949,    945,    936,    926,    920,    918,    920,    924,
      930,    938,    945,    954,    960,    960,    955,    951,
      950,    949,    948,    948,    948,    945,    945,    945,
      948,    943,    942,    937,    937,    937,    939,    945,
      950,    951,    956,    960,    965,    971,    977,    981,
      982,    979,    976,    970,    964,    957,    949,    944,
      942,    942,    945,    950,    955,    955,    957,    960,
      961,    957,    954,    948,    948,    949,    955,    958,
      964,    971,    975,    979,    981,    979,    979,    975,
      973,    971,    970,    969,    969,    969,    969,    973,
      973,    971,    967,    965,    965,    963,    963,    967,
      970,    976,    987,    995,   1001,    996,    993,    987,
      983,    982,    984,    988,    992,    992,    994,    999,
      999,    994,    988,    981,    982,    988,   1002,   1014,
     1020,   1018,   1008,   1000,    994,    996,    997,   1005,
     1009,   1008,   1006,   1002,   1005,   1006,   1012,   1018,
     1024,   1024,   1024,   1024,   1026,   1027,   1029,   1033,
     1035,   1033,   1029,   1026,   1027,   1029,   1035,   1041,
     1047,   1048,   1047,   1048,   1053,   1059,   1072,   1082,
     1086,   1078,   1063,   1047,   1041,   1045,   1057,   1069,
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
    6687,   6702,   6717,   6732,   6748,   6763,   6778,   6793,
    6807,   6822,   6837,   6852,   6866,   6881,   6895,   6910,
    6924,   6939,   6953,   6967,   6981,   6995,   7009,   7023,
    7037,   7051,   7065,   7079,   7093,   7106,   7120,   7133,
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
};

endmodule
