vossstef/tang_nano_20k_c64/src/gowin_prom/gowin_prom_basic.vhd

--Copyright (C)2014-2024 Gowin Semiconductor Corporation.
--All rights reserved.
--File Title: IP file
--Tool Version: V1.9.9.02
--Part Number: GW2AR-LV18QN88C8/I7
--Device: GW2AR-18
--Device Version: C
--Created Time: Thu Apr 25 13:04:41 2024

library IEEE;
use IEEE.std_logic_1164.all;

entity Gowin_pROM_basic is
    port (
        dout: out std_logic_vector(7 downto 0);
        clk: in std_logic;
        oce: in std_logic;
        ce: in std_logic;
        reset: in std_logic;
        ad: in std_logic_vector(12 downto 0)
    );
end Gowin_pROM_basic;

architecture Behavioral of Gowin_pROM_basic is

    signal prom_inst_0_dout_w: std_logic_vector(29 downto 0);
    signal prom_inst_1_dout_w: std_logic_vector(29 downto 0);
    signal prom_inst_2_dout_w: std_logic_vector(29 downto 0);
    signal prom_inst_3_dout_w: std_logic_vector(29 downto 0);
    signal gw_gnd: std_logic;
    signal prom_inst_0_AD_i: std_logic_vector(13 downto 0);
    signal prom_inst_0_DO_o: std_logic_vector(31 downto 0);
    signal prom_inst_1_AD_i: std_logic_vector(13 downto 0);
    signal prom_inst_1_DO_o: std_logic_vector(31 downto 0);
    signal prom_inst_2_AD_i: std_logic_vector(13 downto 0);
    signal prom_inst_2_DO_o: std_logic_vector(31 downto 0);
    signal prom_inst_3_AD_i: std_logic_vector(13 downto 0);
    signal prom_inst_3_DO_o: std_logic_vector(31 downto 0);

    --component declaration
    component pROM
        generic (
            READ_MODE: in bit :='0';
            BIT_WIDTH: in integer := 1;
            RESET_MODE: in string := "SYNC";
            INIT_RAM_00: in bit_vector := X"0000000000000000000000000000000000000000000000000000000000000000";
            INIT_RAM_01: in bit_vector := X"0000000000000000000000000000000000000000000000000000000000000000";
            INIT_RAM_02: in bit_vector := X"0000000000000000000000000000000000000000000000000000000000000000";
            INIT_RAM_03: in bit_vector := X"0000000000000000000000000000000000000000000000000000000000000000";
            INIT_RAM_04: in bit_vector := X"0000000000000000000000000000000000000000000000000000000000000000";
            INIT_RAM_05: in bit_vector := X"0000000000000000000000000000000000000000000000000000000000000000";
            INIT_RAM_06: in bit_vector := X"0000000000000000000000000000000000000000000000000000000000000000";
            INIT_RAM_07: in bit_vector := X"0000000000000000000000000000000000000000000000000000000000000000";
            INIT_RAM_08: in bit_vector := X"0000000000000000000000000000000000000000000000000000000000000000";
            INIT_RAM_09: in bit_vector := X"0000000000000000000000000000000000000000000000000000000000000000";
            INIT_RAM_0A: in bit_vector := X"0000000000000000000000000000000000000000000000000000000000000000";
            INIT_RAM_0B: in bit_vector := X"0000000000000000000000000000000000000000000000000000000000000000";
            INIT_RAM_0C: in bit_vector := X"0000000000000000000000000000000000000000000000000000000000000000";
            INIT_RAM_0D: in bit_vector := X"0000000000000000000000000000000000000000000000000000000000000000";
            INIT_RAM_0E: in bit_vector := X"0000000000000000000000000000000000000000000000000000000000000000";
            INIT_RAM_0F: in bit_vector := X"0000000000000000000000000000000000000000000000000000000000000000";
            INIT_RAM_10: in bit_vector := X"0000000000000000000000000000000000000000000000000000000000000000";
            INIT_RAM_11: in bit_vector := X"0000000000000000000000000000000000000000000000000000000000000000";
            INIT_RAM_12: in bit_vector := X"0000000000000000000000000000000000000000000000000000000000000000";
            INIT_RAM_13: in bit_vector := X"0000000000000000000000000000000000000000000000000000000000000000";
            INIT_RAM_14: in bit_vector := X"0000000000000000000000000000000000000000000000000000000000000000";
            INIT_RAM_15: in bit_vector := X"0000000000000000000000000000000000000000000000000000000000000000";
            INIT_RAM_16: in bit_vector := X"0000000000000000000000000000000000000000000000000000000000000000";
            INIT_RAM_17: in bit_vector := X"0000000000000000000000000000000000000000000000000000000000000000";
            INIT_RAM_18: in bit_vector := X"0000000000000000000000000000000000000000000000000000000000000000";
            INIT_RAM_19: in bit_vector := X"0000000000000000000000000000000000000000000000000000000000000000";
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
        )
        port map (
            DO => prom_inst_3_DO_o,
            CLK => clk,
            OCE => oce,
            CE => ce,
            RESET => reset,
            AD => prom_inst_3_AD_i
        );

end Behavioral; --Gowin_pROM_basic
