vossstef/tang_nano_20k_c64/src/gowin_sdpb/gowin_sdpb_kernal_8k.vhd

--Copyright (C)2014-2024 Gowin Semiconductor Corporation.
--All rights reserved.
--File Title: IP file
--Tool Version: V1.9.9.02
--Part Number: GW2AR-LV18QN88C8/I7
--Device: GW2AR-18
--Device Version: C
--Created Time: Thu Apr 25 13:22:34 2024

library IEEE;
use IEEE.std_logic_1164.all;

entity Gowin_SDPB_kernal_8k is
    port (
        dout: out std_logic_vector(7 downto 0);
        clka: in std_logic;
        cea: in std_logic;
        reseta: in std_logic;
        clkb: in std_logic;
        ceb: in std_logic;
        resetb: in std_logic;
        oce: in std_logic;
        ada: in std_logic_vector(12 downto 0);
        din: in std_logic_vector(7 downto 0);
        adb: in std_logic_vector(12 downto 0)
    );
end Gowin_SDPB_kernal_8k;

architecture Behavioral of Gowin_SDPB_kernal_8k is

    signal sdpb_inst_0_dout_w: std_logic_vector(29 downto 0);
    signal sdpb_inst_1_dout_w: std_logic_vector(29 downto 0);
    signal sdpb_inst_2_dout_w: std_logic_vector(29 downto 0);
    signal sdpb_inst_3_dout_w: std_logic_vector(29 downto 0);
    signal gw_gnd: std_logic;
    signal sdpb_inst_0_BLKSELA_i: std_logic_vector(2 downto 0);
    signal sdpb_inst_0_BLKSELB_i: std_logic_vector(2 downto 0);
    signal sdpb_inst_0_ADA_i: std_logic_vector(13 downto 0);
    signal sdpb_inst_0_DI_i: std_logic_vector(31 downto 0);
    signal sdpb_inst_0_ADB_i: std_logic_vector(13 downto 0);
    signal sdpb_inst_0_DO_o: std_logic_vector(31 downto 0);
    signal sdpb_inst_1_BLKSELA_i: std_logic_vector(2 downto 0);
    signal sdpb_inst_1_BLKSELB_i: std_logic_vector(2 downto 0);
    signal sdpb_inst_1_ADA_i: std_logic_vector(13 downto 0);
    signal sdpb_inst_1_DI_i: std_logic_vector(31 downto 0);
    signal sdpb_inst_1_ADB_i: std_logic_vector(13 downto 0);
    signal sdpb_inst_1_DO_o: std_logic_vector(31 downto 0);
    signal sdpb_inst_2_BLKSELA_i: std_logic_vector(2 downto 0);
    signal sdpb_inst_2_BLKSELB_i: std_logic_vector(2 downto 0);
    signal sdpb_inst_2_ADA_i: std_logic_vector(13 downto 0);
    signal sdpb_inst_2_DI_i: std_logic_vector(31 downto 0);
    signal sdpb_inst_2_ADB_i: std_logic_vector(13 downto 0);
    signal sdpb_inst_2_DO_o: std_logic_vector(31 downto 0);
    signal sdpb_inst_3_BLKSELA_i: std_logic_vector(2 downto 0);
    signal sdpb_inst_3_BLKSELB_i: std_logic_vector(2 downto 0);
    signal sdpb_inst_3_ADA_i: std_logic_vector(13 downto 0);
    signal sdpb_inst_3_DI_i: std_logic_vector(31 downto 0);
    signal sdpb_inst_3_ADB_i: std_logic_vector(13 downto 0);
    signal sdpb_inst_3_DO_o: std_logic_vector(31 downto 0);

    --component declaration
    component SDPB
        generic (
            READ_MODE: in bit := '0';
            BIT_WIDTH_0: in integer :=16;
            BIT_WIDTH_1: in integer :=16;
            BLK_SEL_0: in bit_vector := "000";
            BLK_SEL_1: in bit_vector := "000";
            RESET_MODE: in string := "SYNC";
            INIT_RAM_00: in bit_vector := X"0000000000000000000000000000000000000000000000000000000000000000";
            INIT_RAM_01: in bit_vector := X"0000000000000000000000000000000000000000000000000000000000000000";
            INIT_RAM_02: in bit_vector := X"0000000000000000000000000000000000000000000000000000000000000000";
            INIT_RAM_03: in bit_vector := X"0000000000000000000000000000000000000000000000000000000000000000";
            INIT_RAM_04: in bit_vector := X"0000000000000000000000000000000000000000000000000000000000000000";
            INIT_RAM_05: in bit_vector := X"0000000000000000000000000000000000000000000000000000000000000000";
            INIT_RAM_06: in bit_vector := X"0000000000000000000000000000000000000000000000000000000000000000";
            INIT_RAM_07: in bit_vector := X"0000000000000000000000000000000000000000000000000000000000000000";
            INIT_RAM_08: in bit_vector := X"0000000000000000000000000000000000000000000000000000000000000000";
            INIT_RAM_09: in bit_vector := X"0000000000000000000000000000000000000000000000000000000000000000";
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
            BLKSELB: in std_logic_vector(2 downto 0);
            ADA: in std_logic_vector(13 downto 0);
            DI: in std_logic_vector(31 downto 0);
            ADB: in std_logic_vector(13 downto 0)
        );
    end component;

begin
    gw_gnd <= '0';

    sdpb_inst_0_BLKSELA_i <= gw_gnd & gw_gnd & gw_gnd;
    sdpb_inst_0_BLKSELB_i <= gw_gnd & gw_gnd & gw_gnd;
    sdpb_inst_0_ADA_i <= ada(12 downto 0) & gw_gnd;
    sdpb_inst_0_DI_i <= gw_gnd & gw_gnd & gw_gnd & gw_gnd & gw_gnd & gw_gnd & gw_gnd & gw_gnd & gw_gnd & gw_gnd & gw_gnd & gw_gnd & gw_gnd & gw_gnd & gw_gnd & gw_gnd & gw_gnd & gw_gnd & gw_gnd & gw_gnd & gw_gnd & gw_gnd & gw_gnd & gw_gnd & gw_gnd & gw_gnd & gw_gnd & gw_gnd & gw_gnd & gw_gnd & din(1 downto 0);
    sdpb_inst_0_ADB_i <= adb(12 downto 0) & gw_gnd;
    dout(1 downto 0) <= sdpb_inst_0_DO_o(1 downto 0) ;
    sdpb_inst_0_dout_w(29 downto 0) <= sdpb_inst_0_DO_o(31 downto 2) ;
    sdpb_inst_1_BLKSELA_i <= gw_gnd & gw_gnd & gw_gnd;
    sdpb_inst_1_BLKSELB_i <= gw_gnd & gw_gnd & gw_gnd;
    sdpb_inst_1_ADA_i <= ada(12 downto 0) & gw_gnd;
    sdpb_inst_1_DI_i <= gw_gnd & gw_gnd & gw_gnd & gw_gnd & gw_gnd & gw_gnd & gw_gnd & gw_gnd & gw_gnd & gw_gnd & gw_gnd & gw_gnd & gw_gnd & gw_gnd & gw_gnd & gw_gnd & gw_gnd & gw_gnd & gw_gnd & gw_gnd & gw_gnd & gw_gnd & gw_gnd & gw_gnd & gw_gnd & gw_gnd & gw_gnd & gw_gnd & gw_gnd & gw_gnd & din(3 downto 2);
    sdpb_inst_1_ADB_i <= adb(12 downto 0) & gw_gnd;
    dout(3 downto 2) <= sdpb_inst_1_DO_o(1 downto 0) ;
    sdpb_inst_1_dout_w(29 downto 0) <= sdpb_inst_1_DO_o(31 downto 2) ;
    sdpb_inst_2_BLKSELA_i <= gw_gnd & gw_gnd & gw_gnd;
    sdpb_inst_2_BLKSELB_i <= gw_gnd & gw_gnd & gw_gnd;
    sdpb_inst_2_ADA_i <= ada(12 downto 0) & gw_gnd;
    sdpb_inst_2_DI_i <= gw_gnd & gw_gnd & gw_gnd & gw_gnd & gw_gnd & gw_gnd & gw_gnd & gw_gnd & gw_gnd & gw_gnd & gw_gnd & gw_gnd & gw_gnd & gw_gnd & gw_gnd & gw_gnd & gw_gnd & gw_gnd & gw_gnd & gw_gnd & gw_gnd & gw_gnd & gw_gnd & gw_gnd & gw_gnd & gw_gnd & gw_gnd & gw_gnd & gw_gnd & gw_gnd & din(5 downto 4);
    sdpb_inst_2_ADB_i <= adb(12 downto 0) & gw_gnd;
    dout(5 downto 4) <= sdpb_inst_2_DO_o(1 downto 0) ;
    sdpb_inst_2_dout_w(29 downto 0) <= sdpb_inst_2_DO_o(31 downto 2) ;
    sdpb_inst_3_BLKSELA_i <= gw_gnd & gw_gnd & gw_gnd;
    sdpb_inst_3_BLKSELB_i <= gw_gnd & gw_gnd & gw_gnd;
    sdpb_inst_3_ADA_i <= ada(12 downto 0) & gw_gnd;
    sdpb_inst_3_DI_i <= gw_gnd & gw_gnd & gw_gnd & gw_gnd & gw_gnd & gw_gnd & gw_gnd & gw_gnd & gw_gnd & gw_gnd & gw_gnd & gw_gnd & gw_gnd & gw_gnd & gw_gnd & gw_gnd & gw_gnd & gw_gnd & gw_gnd & gw_gnd & gw_gnd & gw_gnd & gw_gnd & gw_gnd & gw_gnd & gw_gnd & gw_gnd & gw_gnd & gw_gnd & gw_gnd & din(7 downto 6);
    sdpb_inst_3_ADB_i <= adb(12 downto 0) & gw_gnd;
    dout(7 downto 6) <= sdpb_inst_3_DO_o(1 downto 0) ;
    sdpb_inst_3_dout_w(29 downto 0) <= sdpb_inst_3_DO_o(31 downto 2) ;

    sdpb_inst_0: SDPB
        generic map (
            READ_MODE => '0',
            BIT_WIDTH_0 => 2,
            BIT_WIDTH_1 => 2,
            RESET_MODE => "SYNC",
            BLK_SEL_0 => "000",
            BLK_SEL_1 => "000",
            INIT_RAM_00 => X"1445216085A804D5F21600D120DE21490D113070306524545614C534083054C9",
            INIT_RAM_01 => X"CA8B00E31445644B47A9658C09801780D3164D901926432BC0C30902100E0132",
            INIT_RAM_02 => X"2C9CD03A5091144C361903D38DB10038DB13D245F28030238004D3C038E09210",
            INIT_RAM_03 => X"E18A063860818B28510B41133C590CC24B1CA18E32662274C64DF0E30726707C",
            INIT_RAM_04 => X"44003CA8500C81D32AC628A385A2828E04C50A828530A6E24D070C1240204E28",
            INIT_RAM_05 => X"D473CB68403ADEB590F0260991E03480AB247832370C0C89C276524442408933",
            INIT_RAM_06 => X"1C001EAF4292A0D9B4017E2F003D89DFB30C0081C50CC9F107145C309ADCD677",
            INIT_RAM_07 => X"649661D11DD0B7920D4985C5E3581C444BC041306261E8A0B88F0C030CB0228D",
            INIT_RAM_08 => X"F2A801C568D18DD8CCB137AB390FE0E005411B4DE03400D0A3B400E0ED00EC0A",
            INIT_RAM_09 => X"111475155531404936931761A04562022B7B490B4100A3C90305AA28DD821B35",
            INIT_RAM_0A => X"500B4404DA8C089C25DC80411210611519669986D1876D1D94503290CAC10802",
            INIT_RAM_0B => X"5CCA926860D72CC0BA434CA467800A482D84AC32F41E519D610014D205804843",
            INIT_RAM_0C => X"89D08D5E332A319447020E1802018CEDD5CC120C81D98442B143280030C15040",
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
            OCE => oce,
            BLKSELA => sdpb_inst_3_BLKSELA_i,
            BLKSELB => sdpb_inst_3_BLKSELB_i,
            ADA => sdpb_inst_3_ADA_i,
            DI => sdpb_inst_3_DI_i,
            ADB => sdpb_inst_3_ADB_i
        );

end Behavioral; --Gowin_SDPB_kernal_8k
