vossstef/tang_nano_20k_c64/tb/prim_syn.vhd

-- ===========Oooo==========================================Oooo========
-- =  Copyright (C) 2014-2023 Gowin Semiconductor Technology Co.,Ltd.
-- =                     All rights reserved.
-- =====================================================================
--
--  __      __      __
--  \ \    /  \    / /   [File name   ] prim_syn.vhd
--   \ \  / /\ \  / /    [Description ] GW2A VHDL functional synthesis library
--    \ \/ /  \ \/ /     [Timestamp   ] Thu January 21 11:00:30 2021
--     \  /    \  /      [version     ] 1.9.8
--      \/      \/       
--
-- ===========Oooo==========================================Oooo========


---------------------------package global------------------------------

LIBRARY ieee; 
USE ieee.std_logic_1164.all; 
use IEEE.STD_LOGIC_ARITH.ALL;
use IEEE.STD_LOGIC_UNSIGNED.ALL;

PACKAGE components IS 
   attribute syn_black_box: boolean ;
   attribute syn_black_box of Components : package is true;
   attribute black_box_pad_pin: string;
   attribute syn_noprune : boolean;
   attribute xc_map: string;
   attribute xc_map of Components : package is "lut"; 	
--package glb is
--	signal GSRN : std_logic := '1';
--end glb;
--package body glb 
--end glb;
------------------------------GSR---------------------------------------

COMPONENT GSR 
    PORT (
         GSRI : in std_logic
    );
end COMPONENT;

	attribute syn_black_box of GSR : Component is true;
    attribute syn_noprune of GSR : Component is true;
--------------------------LUT1------------------------------
COMPONENT LUT1 
    GENERIC ( INIT : bit_vector := X"0" );
    PORT (
	 F : out std_logic;
         I0 : in std_logic
    );
end COMPONENT;

attribute syn_black_box of LUT1 : Component is true;
attribute xc_map of LUT1 : component is "lut";
	
--------------------------LUT2 -----------------------------
COMPONENT LUT2 
    GENERIC ( INIT : bit_vector := X"0" );
    PORT (
   	 F : out std_logic;
   	 I0 : in std_logic;
   	 I1 : in std_logic
    );
end COMPONENT;

	attribute syn_black_box of LUT2 : Component is true;
	attribute xc_map of LUT2 : component is "lut";
--------------------------LUT3------------------------------
COMPONENT LUT3 
    GENERIC ( INIT : bit_vector := X"00" );
    PORT (
   	 F : out std_logic;
   	 I0 : in std_logic;
   	 I1 : in std_logic;
   	 I2 : in std_logic
    );
end COMPONENT;
	attribute syn_black_box of LUT3 : Component is true;
	attribute xc_map of LUT3 : component is "lut";
--------------------------LUT4 -----------------------------
COMPONENT LUT4 
    GENERIC ( INIT : bit_vector := X"0000" );
    PORT (
   	 F : out std_logic;
   	 I0 : in std_logic;
   	 I1 : in std_logic;
   	 I2 : in std_logic;
   	 I3 : in std_logic
    );
end COMPONENT;
	attribute syn_black_box of LUT4 : Component is true;
	attribute xc_map of LUT4 : component is "lut";
--------------------------LUT5 -----------------------------
COMPONENT LUT5 
    GENERIC ( INIT : bit_vector := X"00000000" );
    PORT (
   	 F : out std_logic;
   	 I0 : in std_logic;
   	 I1 : in std_logic;
   	 I2 : in std_logic;
   	 I3 : in std_logic;
   	 I4 : in std_logic
    );
end COMPONENT;
	attribute syn_black_box of LUT5 : Component is true;
	attribute xc_map of LUT5 : component is "lut";
--------------------------LUT6 -----------------------------

COMPONENT LUT6 
    GENERIC ( INIT : bit_vector := X"0000000000000000" );
    PORT (
   	 F : out std_logic;
   	 I0 : in std_logic;
   	 I1 : in std_logic;
   	 I2 : in std_logic;
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
	 I5 : in std_logic;
	 I6 : in std_logic;
	 I7 : in std_logic;
	 S0 : in std_logic;
	 S1 : in std_logic;
	 S2 : in std_logic;
	 O : out std_logic
    );
end COMPONENT;
	attribute syn_black_box of MUX8 : Component is true;
--------------------------MUX16-----------------------------

COMPONENT MUX16  
    PORT (
	 I0 : in std_logic;
	 I1 : in std_logic;
	 I2 : in std_logic; 
	 I3 : in std_logic;
	 I4 : in std_logic;
	 I5 : in std_logic;
	 I6 : in std_logic;
	 I7 : in std_logic;
	 I8 : in std_logic;
	 I9 : in std_logic;
	 I10 : in std_logic;
	 I11 : in std_logic;
	 I12 : in std_logic;
	 I13 : in std_logic;
	 I14 : in std_logic;
	 I15 : in std_logic;
	 S0 : in std_logic;
	 S1 : in std_logic;
	 S2 : in std_logic;
	 S3 : in std_logic;
	 O : out std_logic
    );
end COMPONENT;
	attribute syn_black_box of MUX16 : Component is true;
--------------------------MUX32-----------------------------

COMPONENT MUX32  
    PORT (
	 I0 : in std_logic;
	 I1 : in std_logic;
	 I2 : in std_logic; 
	 I3 : in std_logic;
	 I4 : in std_logic;
	 I5 : in std_logic;
	 I6 : in std_logic;
	 I7 : in std_logic;
	 I8 : in std_logic;
	 I9 : in std_logic;
	 I10 : in std_logic;
	 I11 : in std_logic;
	 I12 : in std_logic;
	 I13 : in std_logic;
	 I14 : in std_logic;
	 I15 : in std_logic;
	 I16 : in std_logic;
	 I17 : in std_logic;
	 I18 : in std_logic;
	 I19 : in std_logic;
	 I20 : in std_logic;
	 I21 : in std_logic;
	 I22 : in std_logic;
	 I23:  in std_logic;
	 I24 : in std_logic;
	 I25 : in std_logic;
	 I26 : in std_logic;
	 I27 : in std_logic;
	 I28 : in std_logic;
	 I29 : in std_logic;
	 I30 : in std_logic;
	 I31 : in std_logic; 
	 S0 : in std_logic;
	 S1 : in std_logic;
	 S2 : in std_logic;
	 S3 : in std_logic;
	 S4 : in std_logic;
	 O : out std_logic
    );
end COMPONENT;
	attribute syn_black_box of MUX32 : Component is true;
--------------------------ALU-------------------------------

COMPONENT ALU 
    GENERIC (  
         ADD : INTEGER := 0 ;
       	 SUB : INTEGER := 1 ;
         ADDSUB : INTEGER := 2 ;
       	 NE : INTEGER := 3 ;
       	 GE : INTEGER := 4 ;
	 LE : INTEGER := 5;
       	 CUP : INTEGER := 6 ;
         CDN : INTEGER := 7 ;
         CUPCDN : INTEGER := 8;
	 MULT : INTEGER := 9;
	 ALU_MODE : INTEGER := 0
    );	
    PORT (
	 SUM : OUT std_logic;
	 COUT : OUT std_logic;	
	 I0 : IN std_logic;
	 I1: IN std_logic;
	 I3: IN std_logic;
	 CIN: IN std_logic
    );	
end COMPONENT;
	attribute syn_black_box of ALU : Component is true;
----------------------------DFF ------------------------------

COMPONENT DFF 
    GENERIC ( INIT : bit := '0');	
    PORT (
	 Q : OUT std_logic;	
	 D : IN std_logic;	
	 CLK : IN std_logic
    );	
end COMPONENT;
	attribute syn_black_box of DFF : Component is true;
---------------------------DFFE ---------------------------------

COMPONENT DFFE 
    GENERIC ( INIT : bit := '0' );	
    PORT (
	 Q : OUT std_logic;	
	 D : IN std_logic;
	 CE : IN std_logic;	
	 CLK : IN std_logic
    );	
end COMPONENT;
	attribute syn_black_box of DFFE : Component is true;
-------------------------DFFS ---------------------------------

COMPONENT DFFS 
    GENERIC ( INIT: bit := '1' );	
    PORT (
	 Q : OUT std_logic;	
	 D : IN std_logic;
	 SET : IN std_logic;	
	 CLK : IN std_logic
    );	
end COMPONENT;
	attribute syn_black_box of DFFS : Component is true;
----------------------------DFFSE--------------------------------------

COMPONENT DFFSE 
    GENERIC ( INIT : bit := '1' );	
    PORT (
	 Q : OUT std_logic;	
	 D : IN std_logic;
	 SET : IN std_logic;
	 CE: IN std_logic;	
	 CLK : IN std_logic
    );	
end COMPONENT;
	attribute syn_black_box of DFFSE : Component is true;
------------------------DFFR ----------------------------------

COMPONENT DFFR 
    GENERIC ( INIT : bit := '0' );	
    PORT (
	 Q : OUT std_logic;	
	 D : IN std_logic;
	 RESET : IN std_logic;	
	 CLK : IN std_logic
    );	
end COMPONENT;
	attribute syn_black_box of DFFR : Component is true;
---------------------------DFFRE -------------------------------------

COMPONENT DFFRE 
    GENERIC ( INIT : bit := '0' );	
    PORT (
	 Q : OUT std_logic;	
	 D : IN std_logic;
	 RESET : IN std_logic;
	 CE: IN std_logic;	
	 CLK : IN std_logic
    );	
end COMPONENT;
	attribute syn_black_box of DFFRE : Component is true;
----------------------------DFFP---------------------------------------

COMPONENT DFFP 
    GENERIC ( INIT : bit := '1' );	
    PORT (
	 Q : OUT std_logic;	
	 D : IN std_logic;
	 PRESET: IN std_logic;	
	 CLK : IN std_logic
    );	
end COMPONENT;
	attribute syn_black_box of DFFP : Component is true;
--------------------------DFFPE ---------------------------------------------

COMPONENT DFFPE 
    GENERIC ( INIT : bit := '1' );	
    PORT (
	 Q : OUT std_logic;	
	 D : IN std_logic;
	 PRESET : IN std_logic;
	 CE: IN std_logic;	
	 CLK : IN std_logic
    );	
end COMPONENT;
	attribute syn_black_box of DFFPE : Component is true;
-----------------------------DFFC --------------------------------

COMPONENT DFFC 
    GENERIC ( INIT : bit := '0' );	
    PORT (
	 Q : OUT std_logic;	
	 D : IN std_logic;
	 CLEAR : IN std_logic;	
	 CLK : IN std_logic
    );	
end COMPONENT;
	attribute syn_black_box of DFFC : Component is true;
-----------------------------DFFCE -------------------------------------------

COMPONENT DFFCE 
    GENERIC ( INIT : bit := '0' );	
    PORT (
	 Q : OUT std_logic;	
	 D : IN std_logic;
	 CLEAR : IN std_logic;
	 CE: IN std_logic;	
	 CLK : IN std_logic
    );	
end COMPONENT;
	attribute syn_black_box of DFFCE : Component is true;
--------------------------DFFN ------------------------------

COMPONENT DFFN 
    GENERIC ( INIT : bit := '0');	
    PORT (
	 Q : OUT std_logic;	
	 D : IN std_logic;	
	 CLK : IN std_logic
    );	
end COMPONENT;
	attribute syn_black_box of DFFN : Component is true;
------------------DFFNE ---------------------------------

COMPONENT DFFNE 
    GENERIC ( INIT : bit := '0' );	
    PORT (
	 Q : OUT std_logic;	
	 D : IN std_logic;
	 CE : IN std_logic;	
	 CLK : IN std_logic
    );	
end COMPONENT;
	attribute syn_black_box of DFFNE : Component is true;
-------------------------DFFNS ---------------------------------

COMPONENT DFFNS 
    GENERIC ( INIT: bit := '1' );	
    PORT (
	 Q : OUT std_logic;	
	 D : IN std_logic;
	 SET : IN std_logic;	
	 CLK : IN std_logic
    );	
end COMPONENT;
	attribute syn_black_box of DFFNS : Component is true;
----------------------------DFFNSE--------------------------------------

COMPONENT DFFNSE 
    GENERIC ( INIT : bit := '1' );	
    PORT (
	 Q : OUT std_logic;	
	 D : IN std_logic;
	 SET : IN std_logic;
	 CE: IN std_logic;	
	 CLK : IN std_logic
    );	
end COMPONENT;
	attribute syn_black_box of DFFNSE : Component is true;
-----------------------------DFFNR----------------------------------

COMPONENT DFFNR 
    GENERIC ( INIT : bit := '0' );	
    PORT (
	 Q : OUT std_logic;	
	 D : IN std_logic;
	 RESET : IN std_logic;	
	 CLK : IN std_logic
    );	
end COMPONENT;
	attribute syn_black_box of DFFNR : Component is true;
---------------------------DFFNRE -------------------------------------

COMPONENT DFFNRE 
    GENERIC ( INIT : bit := '0' );	
    PORT (
	 Q : OUT std_logic;	
	 D : IN std_logic;
	 RESET : IN std_logic;
	 CE: IN std_logic;	
	 CLK : IN std_logic
    );	
end COMPONENT;
	attribute syn_black_box of DFFNRE : Component is true;
----------------------------DFFNP---------------------------------------

COMPONENT DFFNP 
    GENERIC ( INIT : bit := '1' );	
    PORT (
	 Q : OUT std_logic;	
	 D : IN std_logic;
	 PRESET: IN std_logic;	
	 CLK : IN std_logic
    );	
end COMPONENT;
	attribute syn_black_box of DFFNP : Component is true;
--------------------------DFFNPE ---------------------------------------------

COMPONENT DFFNPE 
    GENERIC ( INIT : bit := '1' );	
    PORT (
	 Q : OUT std_logic;	
	 D : IN std_logic;
	 PRESET : IN std_logic;
	 CE: IN std_logic;	
	 CLK : IN std_logic
    );	
end COMPONENT;
	attribute syn_black_box of DFFNPE : Component is true;
-----------------------------DFFNC --------------------------------------------

COMPONENT DFFNC 
    GENERIC ( INIT : bit := '0' );	
    PORT (
	 Q : OUT std_logic;	
	 D : IN std_logic;
	 CLEAR : IN std_logic;	
	 CLK : IN std_logic
    );	
end COMPONENT;
	attribute syn_black_box of DFFNC : Component is true;
-----------------------------DFFNCE -------------------------------------------

COMPONENT DFFNCE 
    GENERIC ( INIT : bit := '0' );	
    PORT (
	 Q : OUT std_logic;	
	 D : IN std_logic;
	 CLEAR : IN std_logic;
	 CE: IN std_logic;	
	 CLK : IN std_logic
    );	
end COMPONENT;
	attribute syn_black_box of DFFNCE : Component is true;
--------------------------------DL ------------------------------------------

COMPONENT DL 
    GENERIC ( INIT : bit := '0' );	
    PORT (
	 Q : OUT std_logic;	
	 D : IN std_logic;	
	 G : IN std_logic
    );	
end COMPONENT;
	attribute syn_black_box of DL : Component is true;
-------------------------DLE-----------------------------------

COMPONENT DLE 
    GENERIC ( INIT : bit := '0' );	
    PORT (
	 Q : OUT std_logic;	
	 D : IN std_logic;
	 CE: IN std_logic;	
	 G : IN std_logic
    );	
end COMPONENT;
	attribute syn_black_box of DLE : Component is true;
-----------------------------DLC ------------------------------------

COMPONENT DLC 
    GENERIC ( INIT : bit := '0' );	
    PORT (
	 Q : OUT std_logic;	
	 D : IN std_logic;
	 CLEAR : IN std_logic;	
	 G : IN std_logic
    );	
end COMPONENT;
	attribute syn_black_box of DLC : Component is true;
-----------------------------DLCE ------------------------------------

COMPONENT DLCE 
    GENERIC ( INIT : bit := '0' );	
    PORT (
	 Q : OUT std_logic;	
	 D : IN std_logic;
	 CLEAR : IN std_logic;	
	 G : IN std_logic;
	 CE: IN std_logic
    );	
end COMPONENT;
	attribute syn_black_box of DLCE : Component is true;
-----------------------------DLP ------------------------------------

COMPONENT DLP 
    GENERIC ( INIT : bit := '1' );	
    PORT (
	 Q : OUT std_logic;	
	 D : std_logic;
	 PRESET : IN std_logic;	
	 G: IN std_logic
    );	
end COMPONENT;
	attribute syn_black_box of DLP : Component is true;
-----------------------------DLPE ------------------------------------

COMPONENT DLPE 
    GENERIC ( INIT : bit := '1' );	
    PORT (
	 Q : OUT std_logic;	
	 D : IN std_logic;
	 PRESET : IN std_logic;	
	 G : IN std_logic;
	 CE: IN std_logic
    );	
end COMPONENT;
	attribute syn_black_box of DLPE : Component is true;
------------------------DLN ------------------------------------------

COMPONENT DLN 
    GENERIC ( INIT : bit := '0' );	
    PORT (
	 Q : OUT std_logic;	
	 D : IN std_logic;	
	 G : IN std_logic
    );	
end COMPONENT;
	attribute syn_black_box of DLN : Component is true;
-----------------------------DLNE-----------------------------------

COMPONENT DLNE 
    GENERIC ( INIT : bit := '0' );	
    PORT (
	 Q : OUT std_logic;	
	 D : IN std_logic;
	 CE: IN std_logic;	
	 G : IN std_logic
    );	
end COMPONENT;
	attribute syn_black_box of DLNE : Component is true;
-----------------------------DLNC ------------------------------------

COMPONENT DLNC 
    GENERIC ( INIT : bit := '0' );	
    PORT (
	 Q : OUT std_logic;	
	 D : IN std_logic;
	 CLEAR : IN std_logic;	
	 G : IN std_logic
    );	
end COMPONENT;
	attribute syn_black_box of DLNC : Component is true;
-----------------------------DLNCE ------------------------------------

COMPONENT DLNCE 
    GENERIC ( INIT : bit := '0' );	
    PORT (
	 Q : OUT std_logic;	
	 D : IN std_logic;
	 CLEAR : IN std_logic;	
	 G : IN std_logic;
	 CE: IN std_logic
    );	
end COMPONENT;
	attribute syn_black_box of DLNCE : Component is true;
-----------------------------DLNP ------------------------------------

COMPONENT DLNP 
    GENERIC ( INIT : bit := '1' );	
    PORT (
	 Q : OUT std_logic;	
	 D : std_logic;
	 PRESET : IN std_logic;	
	 G: IN std_logic
    );	
end COMPONENT;
	attribute syn_black_box of DLNP : Component is true;
-----------------------------DLNPE ------------------------------------

COMPONENT DLNPE 
    GENERIC ( INIT : bit := '1' );	
    PORT (
	 Q : OUT std_logic;	
	 D : IN std_logic;
	 PRESET : IN std_logic;	
	 G : IN std_logic;
	 CE: IN std_logic
    );	
end COMPONENT;
	attribute syn_black_box of DLNPE : Component is true;
----------------------IBUF-------------------------------------

COMPONENT IBUF 
    PORT (
    	 O : OUT std_logic;
    	 I : IN std_logic
    );
end COMPONENT;
	attribute syn_black_box of IBUF : Component is true;
------------------------------OBUF---------------------------------------

COMPONENT OBUF 
    PORT (
    	 O : OUT std_logic;
    	 I : IN std_logic
    );
end COMPONENT;
	attribute syn_black_box of OBUF : Component is true;
------------------------------------TBUF---------------------------

COMPONENT TBUF 
    PORT (
    	 O : OUT std_logic;
    	 I : IN std_logic;
    	 OEN : IN std_logic
    );
end COMPONENT;
	attribute syn_black_box of TBUF : Component is true;
    attribute black_box_pad_pin of TBUF : Component is "O";

----------------------------IOBUF--------------------------------

COMPONENT IOBUF
    PORT (
    	O  : OUT   std_logic;
    	IO : INOUT std_logic;
     	I  : IN    std_logic;
	    OEN : IN    std_logic
    );
end COMPONENT;
	attribute syn_black_box of IOBUF : Component is true;
---------------------------------IDDR--------------------------

COMPONENT IDDR 
    GENERIC (
	Q0_INIT : bit := '0';
	Q1_INIT : bit := '0'
    );	
    PORT (
	 Q0 : OUT std_logic;
	 Q1 : OUT std_logic;	
	 D : IN std_logic;
	 CLK: IN std_logic
    );	
end COMPONENT;
	attribute syn_black_box of IDDR : Component is true;

---------------------------------IDDRC---------------------------

COMPONENT IDDRC 
    GENERIC ( 
	Q0_INIT : bit := '0';
	Q1_INIT : bit := '0'
    );	
    PORT (
	 Q0 : OUT std_logic;
	 Q1 : OUT std_logic;	
	 D : IN std_logic;
	 CLEAR: IN std_logic;	
	 CLK: IN std_logic
    );	
end COMPONENT;
	attribute syn_black_box of IDDRC : Component is true;

----------------------------IDDR_MEM------------------------------------

COMPONENT IDDR_MEM 
	GENERIC (
		GSREN : string := "false";
		LSREN  : string := "true"
	);
	PORT (
		Q0 : out std_logic;	
		Q1 : out std_logic;	
		D : in std_logic;
		ICLK : in std_logic;
		PCLK : in std_logic;
		RESET : in std_logic;
		WADDR : in std_logic_vector(2 downto 0);
	   	RADDR : in std_logic_vector(2 downto 0)
	);
end COMPONENT;
	attribute syn_black_box of IDDR_MEM : Component is true;

-------------------------------ODDR----------------------
COMPONENT ODDR 
    GENERIC ( 
        TXCLK_POL : bit := '0'; --'0':Rising edge output; '1':Falling edge output        
        CONSTANT INIT : std_logic := '0' 
    );	
    PORT ( 
	    Q0 : OUT std_logic;	
	    Q1 : OUT std_logic;	
	    D0 : IN std_logic;
	    D1 : IN std_logic;
	    TX : IN std_logic;
	    CLK : IN std_logic
    );	
end COMPONENT;
	attribute syn_black_box of ODDR : Component is true;

-------------------------------ODDRC----------------------

COMPONENT ODDRC 
    GENERIC ( 
        TXCLK_POL : bit := '0'; --'0':Rising edge output; '1':Falling edge output
        CONSTANT INIT : std_logic := '0'
    );
    PORT (
	    Q0 : OUT std_logic;
	    Q1 : OUT std_logic;
	    D0 : IN std_logic;
	    D1 : IN std_logic;
	    TX : IN std_logic;
	    CLK : IN std_logic;
	    CLEAR : IN std_logic
    );	
end COMPONENT;
	attribute syn_black_box of ODDRC : Component is true;

----------------------------ODDR_MEM------------------------------------
COMPONENT ODDR_MEM 
    GENERIC(
		GSREN : string := "false";
		LSREN  : string := "true";
        TXCLK_POL : bit := '0'; --'0':Rising edge output; '1':Falling edge output
        TCLK_SOURCE : string := "DQSW"
    );
    PORT (
		 Q0 : out std_logic;	
		 Q1 : out std_logic;	
		 TCLK : in std_logic;
		 PCLK : in std_logic;
		 RESET : in std_logic;
		 D0 : in std_logic;
		 D1 : in std_logic;
		 TX : in std_logic
    );
end COMPONENT;
	attribute syn_black_box of ODDR_MEM : Component is true;
-----------------------------------------IDES4-------------------------------

COMPONENT IDES4 
	GENERIC (
		GSREN : string := "false";
		LSREN  : string := "true"
	);
	PORT (
		D : IN std_logic;
		CALIB : IN std_logic;
		RESET : IN std_logic;
		FCLK : IN std_logic;
		PCLK : IN std_logic;
		Q0 : OUT std_logic;
		Q1 : OUT std_logic;
		Q2 : OUT std_logic;
		Q3 : OUT std_logic
	);
end COMPONENT;
	attribute syn_black_box of IDES4 : Component is true;
--------------------------IDES4_MEM----------------------------------

COMPONENT IDES4_MEM 
	generic(
		GSREN : string := "false";
		LSREN  : string := "true"
	);
	PORT(
		D,RESET : IN std_logic;
		CALIB : IN std_logic;
		ICLK,FCLK,PCLK : IN std_logic;
		WADDR : IN std_logic_vector(2 downto 0);
		RADDR : IN std_logic_vector(2 downto 0);
		Q0 : OUT std_logic;
		Q1 : OUT std_logic;
		Q2 : OUT std_logic;
		Q3 : OUT std_logic
	 );
end COMPONENT;
	attribute syn_black_box of IDES4_MEM : Component is true;
------------------------------------IVIDEO-------------------------------

COMPONENT IVIDEO 
    GENERIC (
		GSREN : string := "false";
		LSREN  : string := "true"
    );
    PORT (
		D : IN std_logic;
		RESET : IN std_logic;
		CALIB : IN std_logic;
		FCLK : IN std_logic;
		PCLK : IN std_logic;
		Q0 : OUT std_logic;
		Q1 : OUT std_logic;
		Q2 : OUT std_logic;
		Q3 : OUT std_logic;
		Q4 : OUT std_logic;
		Q5 : OUT std_logic;
		Q6 : OUT std_logic
    );
end COMPONENT;
	attribute syn_black_box of IVIDEO : Component is true;
-----------------------------------IDES8-------------------------------------

COMPONENT IDES8 
    GENERIC (
	    GSREN : string := "false";
		LSREN  : string := "true"
    );
    PORT (
		D,RESET : IN std_logic;
		CALIB : IN std_logic;
		FCLK,PCLK : IN std_logic;
		Q0 : OUT std_logic;
		Q1 : OUT std_logic;
		Q2 : OUT std_logic;
		Q3 : OUT std_logic;
		Q4 : OUT std_logic;
		Q5 : OUT std_logic;
		Q6 : OUT std_logic;
		Q7 : OUT std_logic
    );
end COMPONENT;
	attribute syn_black_box of IDES8 : Component is true;
-------------------------IDES8_MEM----------------------------

COMPONENT IDES8_MEM 
    GENERIC (
	    GSREN : string := "false";
		LSREN  : string := "true"
    );
    PORT (
		D,RESET : IN std_logic;
		CALIB : IN std_logic;
		FCLK,ICLK,PCLK : IN std_logic;
		Q0 : OUT std_logic;
		Q1 : OUT std_logic;
		Q2 : OUT std_logic;
		Q3 : OUT std_logic;
		Q4 : OUT std_logic;
		Q5 : OUT std_logic;
		Q6 : OUT std_logic;
		Q7 : OUT std_logic;
		WADDR : in std_logic_vector(2 downto 0);
		RADDR : in std_logic_vector(2 downto 0)
    );
end COMPONENT;
	attribute syn_black_box of IDES8_MEM : Component is true;
--------------------------------------IDES10----------------------------------

COMPONENT IDES10 
    GENERIC (
	    GSREN : string := "false";
		LSREN  : string := "true"
    );
    PORT (
		D,RESET : IN std_logic;
		CALIB : IN std_logic;
		FCLK,PCLK : IN std_logic;
		Q0 : OUT std_logic;
		Q1 : OUT std_logic;
		Q2 : OUT std_logic;
		Q3 : OUT std_logic;
		Q4 : OUT std_logic;
		Q5 : OUT std_logic;
		Q6 : OUT std_logic;
		Q7 : OUT std_logic;
		Q8 : OUT std_logic;
		Q9 : OUT std_logic
    );
end COMPONENT;
	attribute syn_black_box of IDES10 : Component is true;
-------------------------OSER4------------------------------

COMPONENT OSER4 
	GENERIC (
		GSREN : string := "false";
		LSREN : string := "true";
        HWL : string := "false"; --"true"; "false"
        TXCLK_POL : bit := '0' --'0':Rising edge output; '1':Falling edge output
	);
	PORT (
		D0 : in std_logic;
		D1 : in std_logic;
		D2 : in std_logic;
		D3 : in std_logic;
		TX0 : in std_logic;
		TX1 : in std_logic;
		PCLK : in std_logic;
		RESET : in std_logic;
		FCLK : in std_logic;
		Q0 : OUT std_logic;
		Q1 : OUT std_logic
	);
end COMPONENT;
	attribute syn_black_box of OSER4 : Component is true;
-----------------OSER4_MEM--------------------------------

COMPONENT OSER4_MEM 
	GENERIC (
		GSREN : string := "false";
		LSREN : string := "true";
		HWL : string := "false";
        TXCLK_POL : bit := '0';--'0':Rising edge output; '1':Falling edge output
        TCLK_SOURCE : string := "DQSW"    
	);
	PORT (
		D0 : in std_logic;
		D1 : in std_logic;
		D2 : in std_logic;
		D3 : in std_logic;
		TX0 : in std_logic;
		TX1 : in std_logic;
		PCLK : in std_logic;
		RESET : in std_logic;
		FCLK : in std_logic;
		TCLK : in std_logic;
		Q0 : OUT std_logic;
		Q1 : OUT std_logic
	);
end COMPONENT;
	attribute syn_black_box of OSER4_MEM : Component is true;
--------------------OVIDEO----------------------------------

COMPONENT OVIDEO 
	GENERIC(
		GSREN : string := "false";
		LSREN : string := "true"
	);
	PORT (
		D0 : in std_logic;
		D1 : in std_logic;
		D2 : in std_logic;
		D3 : in std_logic;
		D4 : in std_logic;
		D5 : in std_logic;
		D6 : in std_logic;
		PCLK : in std_logic;
		RESET : in std_logic;
		FCLK : in std_logic;
		Q : OUT std_logic
	);
end COMPONENT;
	attribute syn_black_box of OVIDEO : Component is true;
--------------------OSER8-----------------------------------

COMPONENT OSER8 
    GENERIC (
    	GSREN : string := "false";
    	LSREN : string := "true";
        HWL : string := "false";
        TXCLK_POL : bit := '0' --'0':Rising edge output; '1':Falling edge output
    );
    PORT (
       	D0 : in std_logic;
       	D1 : in std_logic;
       	D2 : in std_logic;
       	D3 : in std_logic;
       	D4 : in std_logic;
      	D5 : in std_logic;
       	D6 : in std_logic;
       	D7 : in std_logic;
       	TX0 : in std_logic;
    	TX1 : in std_logic;
	    TX2 : in std_logic;
	    TX3 : in std_logic;
	    PCLK : in std_logic;
	    RESET : in std_logic;
	    FCLK : in std_logic;
       	Q0 : OUT std_logic;
       	Q1 : OUT std_logic
    );
end COMPONENT;
	attribute syn_black_box of OSER8 : Component is true;
-----------------OSER8_MEM--------------------------------

COMPONENT OSER8_MEM 
	GENERIC(
		GSREN : string := "false";
		LSREN : string := "true";
		HWL : string := "false";
        TXCLK_POL : bit := '0';
        TCLK_SOURCE : string := "DQSW"
	);
	PORT (
		D0 : in std_logic;
		D1 : in std_logic;
		D2 : in std_logic;
		D3 : in std_logic;
		D4 : in std_logic;
		D5 : in std_logic;
		D6 : in std_logic;
		D7 : in std_logic;
		TX0 : in std_logic;
		TX1 : in std_logic;
		TX2 : in std_logic;
		TX3 : in std_logic;
		PCLK : in std_logic;
		RESET : in std_logic;
		FCLK : in std_logic;
		TCLK : in std_logic;
		Q0 : OUT std_logic;
		Q1 : OUT std_logic
	);
end COMPONENT;
	attribute syn_black_box of OSER8_MEM : Component is true;
--------------------OSER10-----------------------------------

COMPONENT OSER10 
	GENERIC (
		GSREN : string := "false";
		LSREN : string := "true"
	);
	PORT (
		D0 : in std_logic;
		D1 : in std_logic;
		D2 : in std_logic;
		D3 : in std_logic;
		D4 : in std_logic;
		D5 : in std_logic;
		D6 : in std_logic;
		D7 : in std_logic;
		D8 : in std_logic;
		D9 : in std_logic;
		PCLK : in std_logic;
		RESET : in std_logic;
		FCLK : in std_logic;
		Q : OUT std_logic
	);
end COMPONENT;
	attribute syn_black_box of OSER10 : Component is true;
--------------------IODELAY-----------------------------------

COMPONENT IODELAY 
	GENERIC (  C_STATIC_DLY : integer := 0); -- 0~127
	PORT (
		DI : IN std_logic;
		SDTAP : IN std_logic;
		SETN : IN std_logic;
		VALUE : IN std_logic;
		DO : OUT std_logic;
		DF : OUT std_logic
	);
end COMPONENT;
	attribute syn_black_box of IODELAY : Component is true;
--------------------IEM----------------------------------

COMPONENT IEM 
	GENERIC(
		WINSIZE : string := "SMALL";
		GSREN : string := "false";
		LSREN  : string := "true"
	);
	PORT (
		D : in std_logic;
		CLK : in std_logic;
		RESET : in std_logic;
		MCLK: in std_logic;
		LAG : out std_logic;
		LEAD : out std_logic
	);
end COMPONENT;
	attribute syn_black_box of IEM : Component is true;
-----------------------ROM----------------------------

COMPONENT ROM 
    GENERIC ( 
	 BIT_WIDTH : integer :=1;	
	 READ_MODE : bit := '0';
     BLK_SEL : bit_vector := "000";
     RESET_MODE : string := "SYNC"; --SYNC, ASYNC
	 INIT_RAM_00 : bit_vector := X"0000000000000000000000000000000000000000000000000000000000000000";
	 INIT_RAM_01 : bit_vector := X"0000000000000000000000000000000000000000000000000000000000000000";
	 INIT_RAM_02 : bit_vector := X"0000000000000000000000000000000000000000000000000000000000000000";
	 INIT_RAM_03 : bit_vector := X"0000000000000000000000000000000000000000000000000000000000000000";
	 INIT_RAM_04 : bit_vector := X"0000000000000000000000000000000000000000000000000000000000000000";
	 INIT_RAM_05 : bit_vector := X"0000000000000000000000000000000000000000000000000000000000000000";
	 INIT_RAM_06 : bit_vector := X"0000000000000000000000000000000000000000000000000000000000000000";
	 INIT_RAM_07 : bit_vector := X"0000000000000000000000000000000000000000000000000000000000000000";
	 INIT_RAM_08 : bit_vector := X"0000000000000000000000000000000000000000000000000000000000000000";
	 INIT_RAM_09 : bit_vector := X"0000000000000000000000000000000000000000000000000000000000000000";
	 INIT_RAM_0A : bit_vector := X"0000000000000000000000000000000000000000000000000000000000000000";
	 INIT_RAM_0B : bit_vector := X"0000000000000000000000000000000000000000000000000000000000000000";
	 INIT_RAM_0C : bit_vector := X"0000000000000000000000000000000000000000000000000000000000000000";
	 INIT_RAM_0D : bit_vector := X"0000000000000000000000000000000000000000000000000000000000000000";
	 INIT_RAM_0E : bit_vector := X"0000000000000000000000000000000000000000000000000000000000000000";
	 INIT_RAM_0F : bit_vector := X"0000000000000000000000000000000000000000000000000000000000000000";
	 INIT_RAM_10 : bit_vector := X"0000000000000000000000000000000000000000000000000000000000000000";
	 INIT_RAM_11 : bit_vector := X"0000000000000000000000000000000000000000000000000000000000000000";
	 INIT_RAM_12 : bit_vector := X"0000000000000000000000000000000000000000000000000000000000000000";
	 INIT_RAM_13 : bit_vector := X"0000000000000000000000000000000000000000000000000000000000000000";
	 INIT_RAM_14 : bit_vector := X"0000000000000000000000000000000000000000000000000000000000000000";
	 INIT_RAM_15 : bit_vector := X"0000000000000000000000000000000000000000000000000000000000000000";
	 INIT_RAM_16 : bit_vector := X"0000000000000000000000000000000000000000000000000000000000000000";
	 INIT_RAM_17 : bit_vector := X"0000000000000000000000000000000000000000000000000000000000000000";
	 INIT_RAM_18 : bit_vector := X"0000000000000000000000000000000000000000000000000000000000000000";
	 INIT_RAM_19 : bit_vector := X"0000000000000000000000000000000000000000000000000000000000000000";
	 INIT_RAM_1A : bit_vector := X"0000000000000000000000000000000000000000000000000000000000000000";
	 INIT_RAM_1B : bit_vector := X"0000000000000000000000000000000000000000000000000000000000000000";
	 INIT_RAM_1C : bit_vector := X"0000000000000000000000000000000000000000000000000000000000000000";
	 INIT_RAM_1D : bit_vector := X"0000000000000000000000000000000000000000000000000000000000000000";
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

    );
    PORT (
	 DO : out std_logic_vector(35 downto 0):=conv_std_logic_vector(0,36);
	 CLK, CE,OCE,RESET,WRE : in std_logic;
    	 BLKSEL : in std_logic_vector(2 downto 0);
	 AD : in std_logic_vector(13 downto 0)
    );
end COMPONENT;
	attribute syn_black_box of ROMX9 : Component is true;
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
