vossstef/tang_nano_20k_c64/src/c1541/gcr_floppy.vhd

---------------------------------------------------------------------------------
-- Commodore 1541 gcr floppy (read/write) by Dar (darfpga@aol.fr) 23-May-2017
-- http://darfpga.blogspot.fr
--
-- produces GCR data, byte(ready) and sync signal to feed c1541_logic from current
-- track buffer ram which contains D64 data
--
-- gets GCR data from c1541_logic, while producing byte(ready) signal. Data feed 
-- track buffer ram after conversion
--
-- Input clk 32MHz
--     
---------------------------------------------------------------------------------
library ieee;
use ieee.std_logic_1164.all;
use ieee.std_logic_unsigned.all;
use ieee.numeric_std.all;

entity gcr_floppy is
port(
	clk32  : in  std_logic;
	c1541_logic_din  : out std_logic_vector(7 downto 0);   -- data from ram to 1541 logic
	c1541_logic_dout : in  std_logic_vector(7 downto 0);   -- data from 1541 logic to ram 
	mode   : in  std_logic;                      -- read/write
--	stp    : in  std_logic_vector(1 downto 0);   -- stepper motor control
	mtr    : in  std_logic;                      -- stepper motor on/off
	freq   : in  std_logic_vector(1 downto 0);   -- motor (gcr_bit) frequency
	sync_n : out std_logic;                      -- reading SYNC bytes
	byte_n : out std_logic;                      -- byte ready
	
	track_num   : in  std_logic_vector(5 downto 0);
	id1         : in  std_logic_vector(7 downto 0);
	id2         : in  std_logic_vector(7 downto 0);
	raw_freq    : in  std_logic_vector(1 downto 0);
	mounted     : in  std_logic;
	raw         : in  std_logic;
	raw_track_len : in  std_logic_vector(15 downto 0);

	ram_addr    : out std_logic_vector(12 downto 0);
	ram_do      : in  std_logic_vector(7 downto 0);
	ram_di      : out std_logic_vector(7 downto 0);
	ram_we      : out std_logic;
	ram_ready   : in  std_logic;
	
	dbg_sector  : out std_logic_vector(4 downto 0)
);
end gcr_floppy;

architecture struct of gcr_floppy is

signal bit_clk_en  : std_logic;
signal bit_clk_div : std_logic_vector(7 downto 0);
signal sync_cnt    : std_logic_vector(5 downto 0) := (others => '0');
signal byte_cnt    : std_logic_vector(8 downto 0) := (others => '0');
signal byte_in     : std_logic_vector(7 downto 0);
signal byte_out    : std_logic_vector(7 downto 0);
signal byte_we     : std_logic;
signal byte_addr   : std_logic_vector(12 downto 0);
signal nibble      : std_logic := '0';
signal gcr_bit_cnt : std_logic_vector(3 downto 0) := (others => '0');
signal bit_cnt     : std_logic_vector(2 downto 0) := (others => '0');

signal sync_in_n   : std_logic;
signal byte_in_n   : std_logic;

signal sector      : std_logic_vector(4 downto 0) := (others => '0');
signal state       : std_logic                    := '0';

signal data_header : std_logic_vector(7 downto 0);
signal data_body   : std_logic_vector(7 downto 0);
signal data        : std_logic_vector(7 downto 0);
signal data_cks    : std_logic_vector(7 downto 0);
signal gcr_nibble  : std_logic_vector(4 downto 0);
signal gcr_bit     : std_logic;
signal gcr_byte    : std_logic_vector(7 downto 0);

signal mode_r1     : std_logic;
signal mode_r2     : std_logic;

signal old_track   : std_logic_vector(5 downto 0);

signal raw_bit_clk_en : std_logic;
signal raw_bit_clk_div: std_logic_vector(7 downto 0);
signal raw_byte_cnt   : std_logic_vector(12 downto 0);
signal raw_bit_cnt    : std_logic_vector( 2 downto 0);
signal raw_byte_in    : std_logic_vector( 7 downto 0);
signal raw_byte_we    : std_logic;
signal synced_bit_cnt : std_logic_vector( 2 downto 0);
signal shift_reg      : std_logic_vector(17 downto 0);
signal sync_in_n_raw  : std_logic;
signal byte_in_n_raw  : std_logic;

type gcr_array is array(0 to 15) of std_logic_vector(4 downto 0);

signal gcr_lut : gcr_array := 
	("01010","11010","01001","11001",
	 "01110","11110","01101","11101",
	 "10010","10011","01011","11011",
	 "10110","10111","01111","10101");
	 
signal sector_max : std_logic_vector(4 downto 0);

signal gcr_byte_out   : std_logic_vector(7 downto 0);
signal gcr_bit_out    : std_logic;
signal gcr_nibble_out : std_logic_vector(4 downto 0);
signal nibble_out     : std_logic_vector(3 downto 0);

signal autorise_write : std_logic;
signal autorise_count : std_logic;

signal lfsr : std_logic_vector(3 downto 0) := "0001";

begin

ram_addr <=       raw_byte_cnt when raw = '1' else byte_addr;
ram_we <=          raw_byte_we when raw = '1' else byte_we;
ram_di <=     c1541_logic_dout when raw = '1' else byte_out;
c1541_logic_din <= raw_byte_in when raw = '1' else byte_in;

sync_n <= '1' when ram_ready = '0' or mtr = '0' else
	sync_in_n_raw when raw = '1' else
	sync_in_n;

dbg_sector <= sector;

with byte_cnt select
  data_header <= 
		X"08"                          when "000000000",
	  "00"&track_num xor "000"&sector xor id1 xor id2 when "000000001",
	  "000"&sector                    when "000000010",
	  "00"&track_num                  when "000000011",
	  id2                             when "000000100",
	  id1                             when "000000101",
	  X"0F"                           when others;
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
